pmgducati/Arcade-Project/Arcade Images/2020-11-22.png

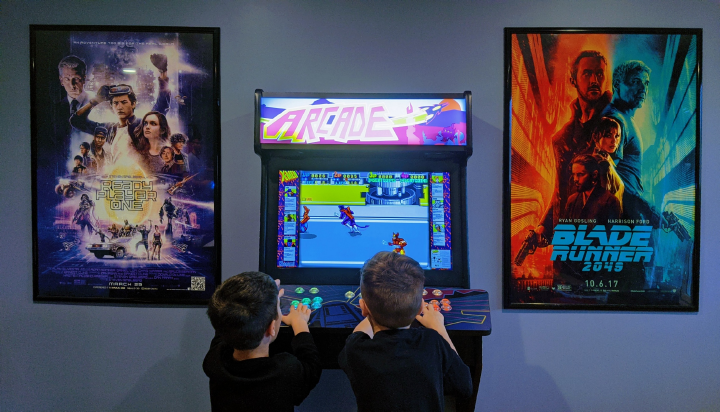
Arcade Images/2020-11-22.png
