pmgducati/Arcade-Project/Arcade Images/Cabinet - Bottom.png

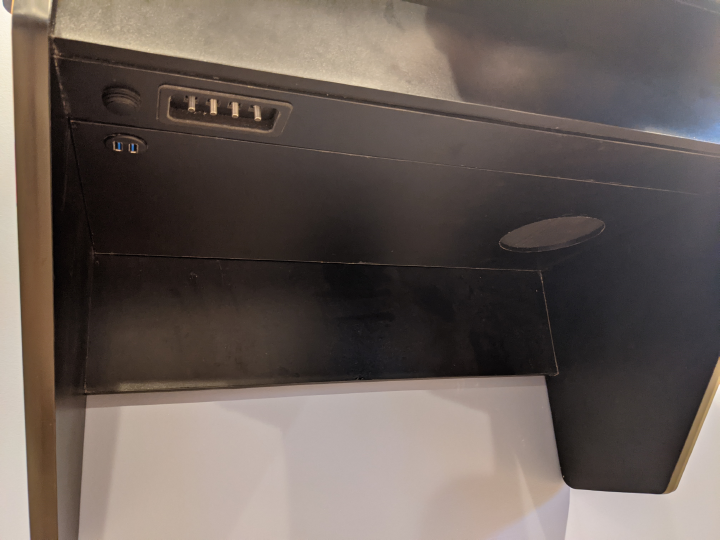
Arcade Images/Cabinet - Bottom.png
