pmgducati/Arcade-Project/Arcade Images/Cabinet - Front.png

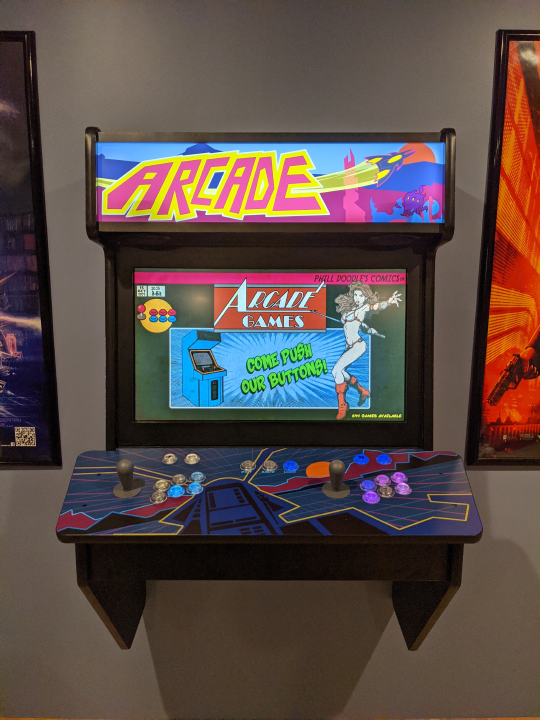
Arcade Images/Cabinet - Front.png
