pmgducati/Arcade-Project/Arcade Images/Cabinet - Left.png

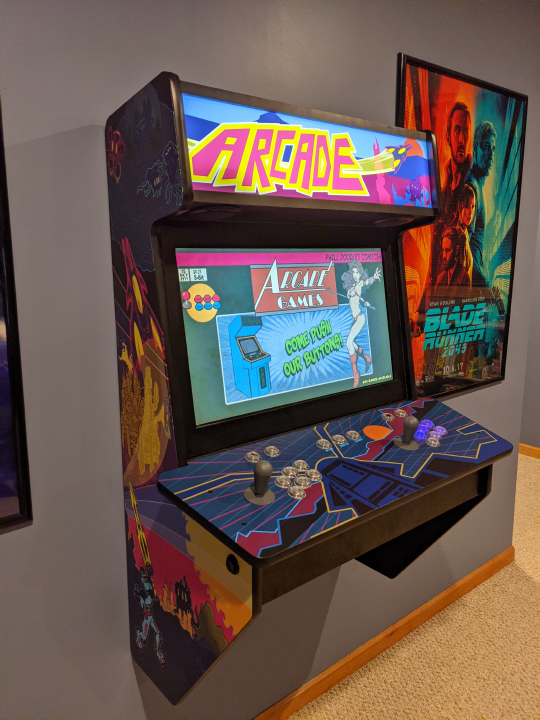
Arcade Images/Cabinet - Left.png
