pmgducati/Arcade-Project/Arcade Images/Cabinet - Right.png

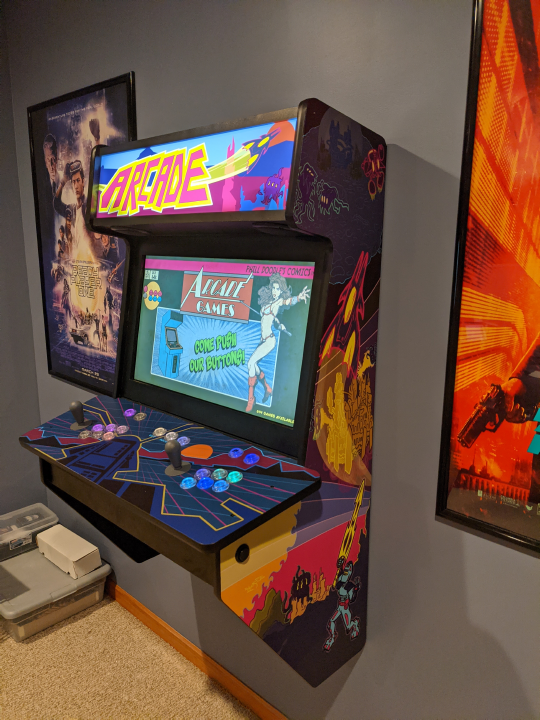
Arcade Images/Cabinet - Right.png
