pmgducati/Arcade-Project/Arcade Images/Cabinet - Top.png

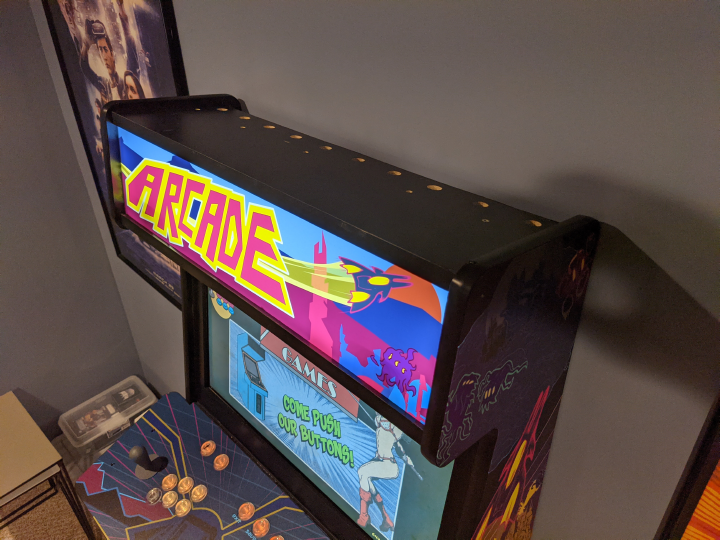
Arcade Images/Cabinet - Top.png
