pmgducati/Arcade-Project/Arcade Images/Control Panel.png

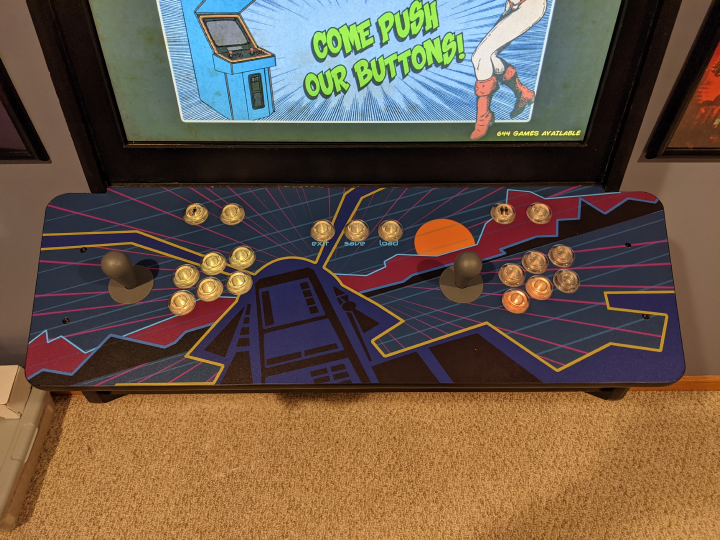
Arcade Images/Control Panel.png
