pmgducati/Arcade-Project/Arcade Images/Marquee.png

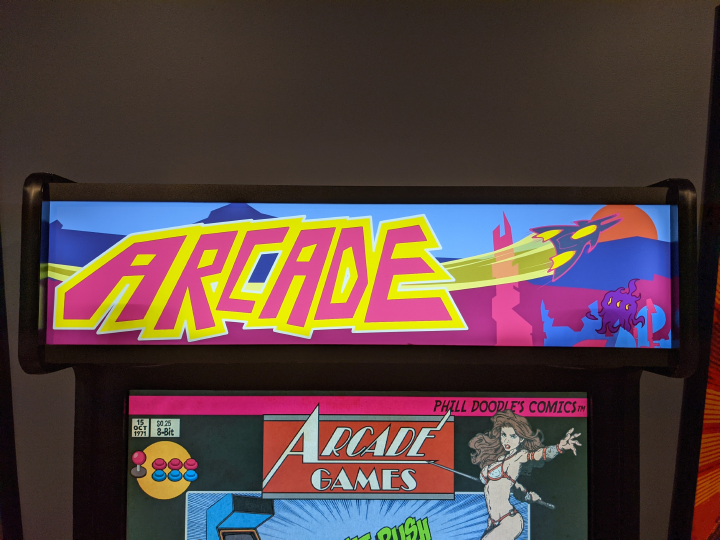
Arcade Images/Marquee.png
