pmgducati/Arcade-Project/Arcade Images/PXL_20201201_182632411.png

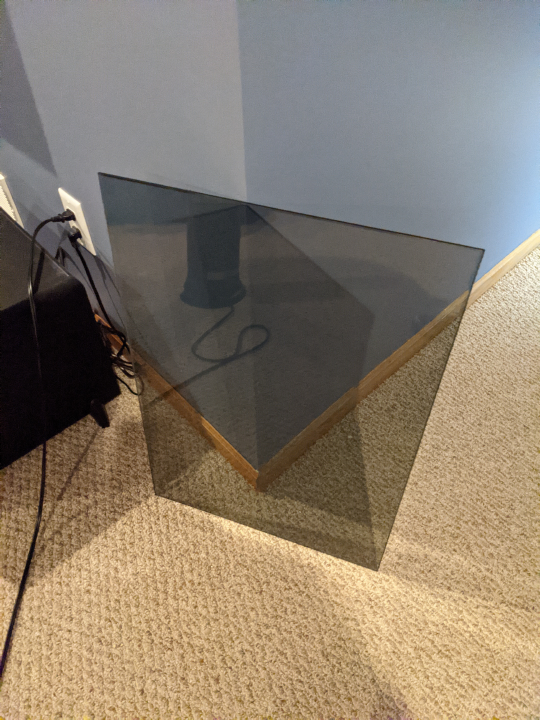
Arcade Images/PXL_20201201_182632411.png
