pmgducati/Arcade-Project/Arcade Images/PXL_20201201_213955558.png

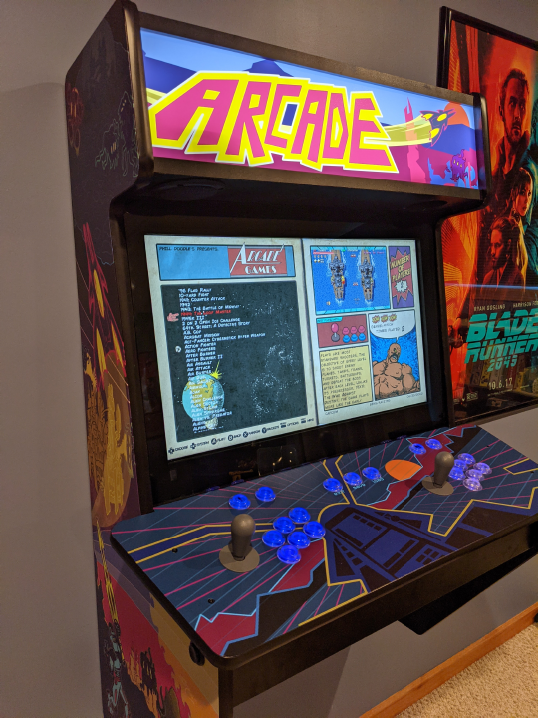
Arcade Images/PXL_20201201_213955558.png
