pmgducati/Arcade-Project/Arcade Images/PXL_20201201_214026619.png

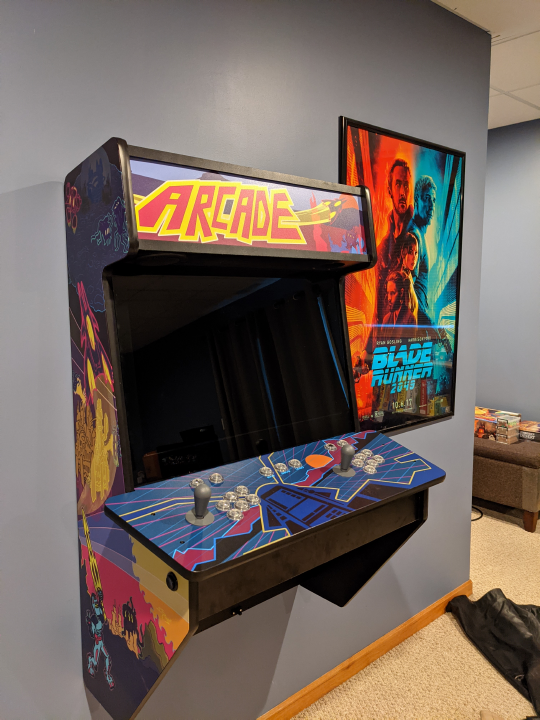
Arcade Images/PXL_20201201_214026619.png
