pmgducati/Arcade-Project/Arcade Images/Under Control Panel 1.png

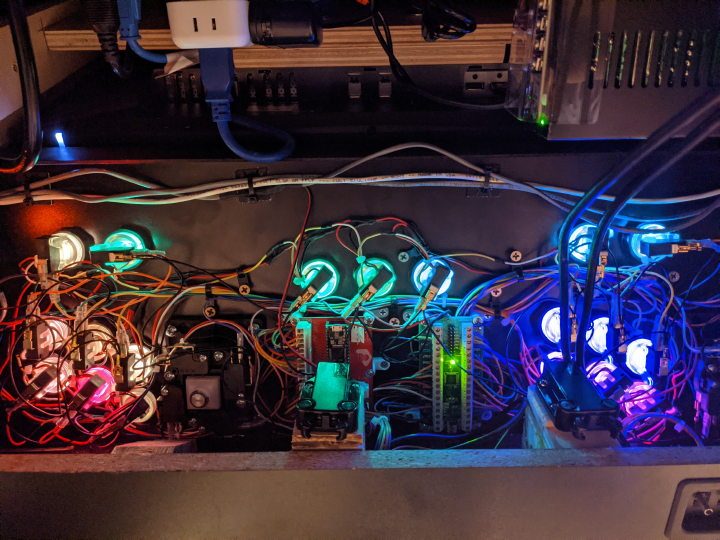
Arcade Images/Under Control Panel 1.png
