pmgducati/Arcade-Project/Arcade Images/Under Control Panel 2.png

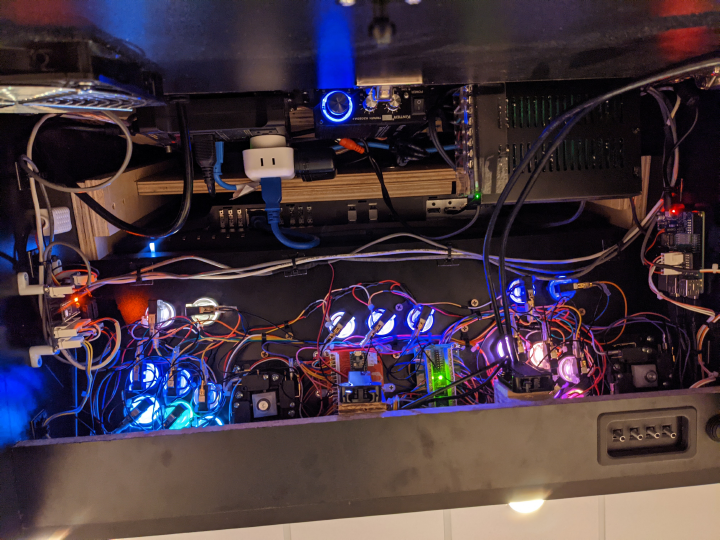
Arcade Images/Under Control Panel 2.png
