pmgducati/Arcade-Project/Art for Inspiration/1.jpg

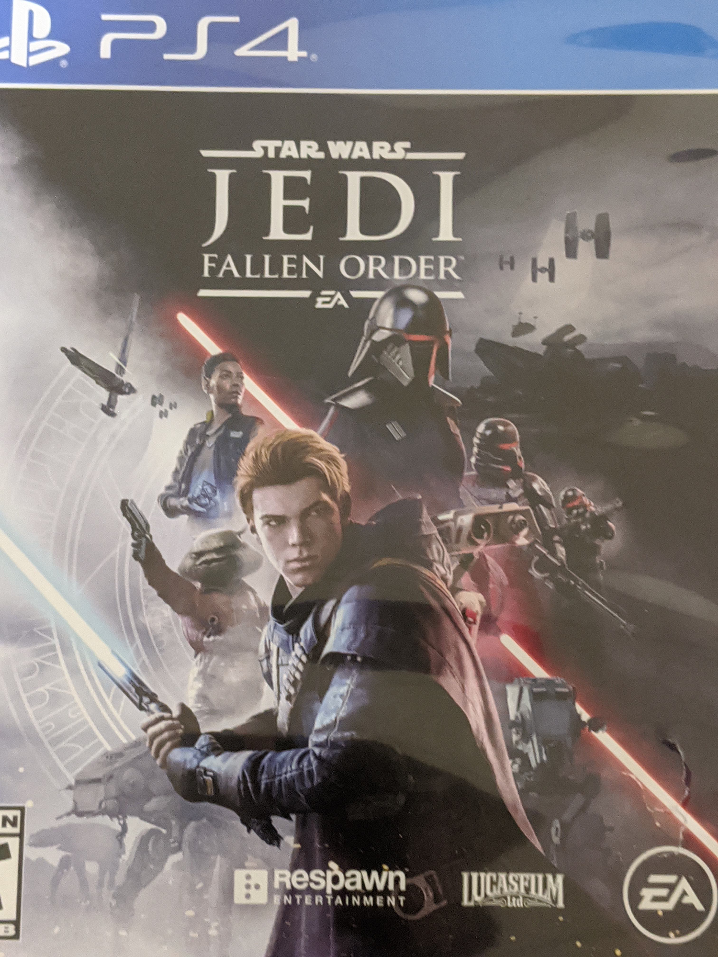
Art for Inspiration/1.jpg
