pmgducati/Arcade-Project/Art for Inspiration/17.png

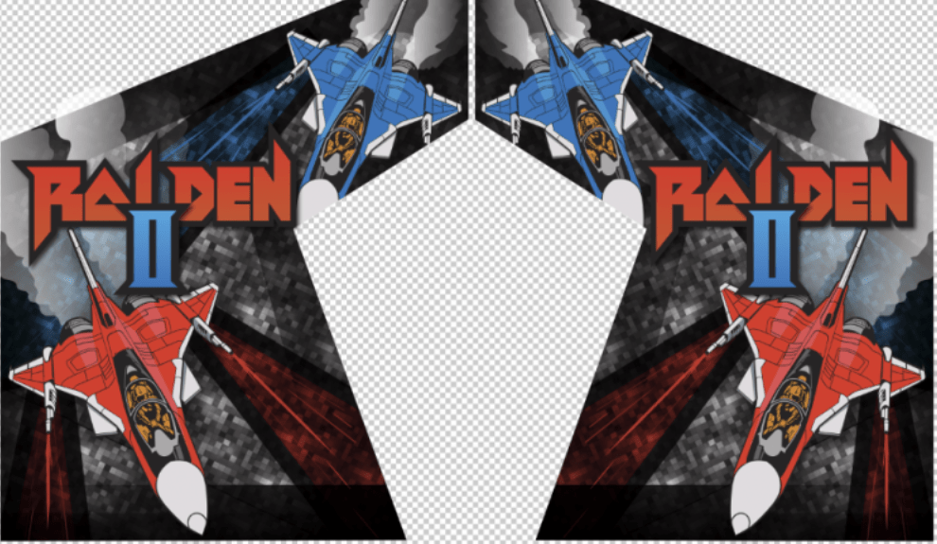
Art for Inspiration/17.png
