pmgducati/Arcade-Project/Art for Inspiration/18.jpg

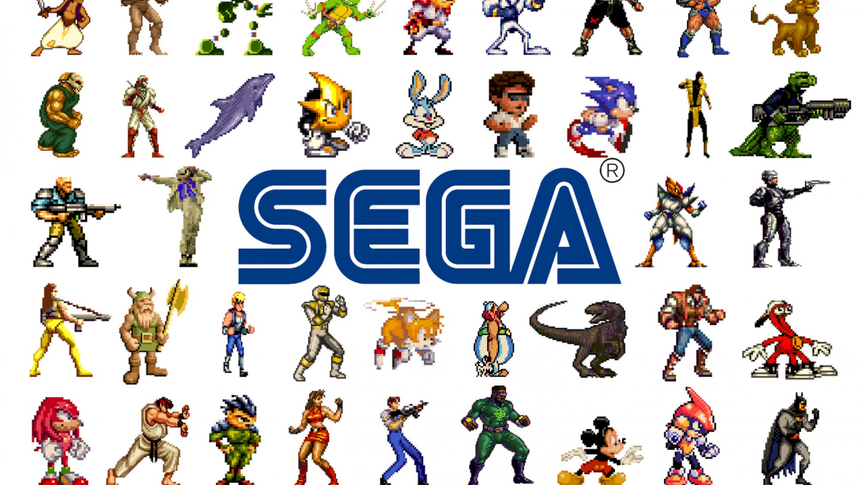
Art for Inspiration/18.jpg
