pmgducati/Arcade-Project/Art for Inspiration/19.jpg

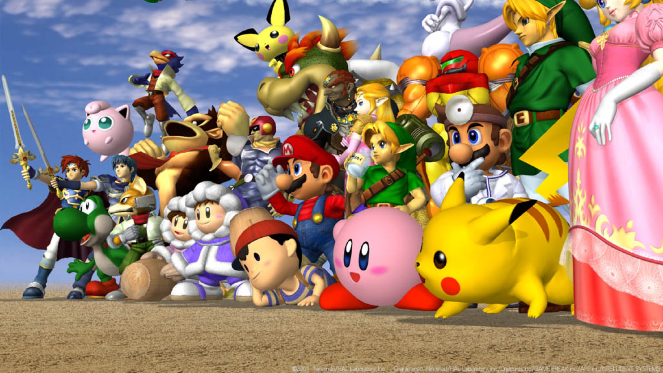
Art for Inspiration/19.jpg
