pmgducati/Arcade-Project/Art for Inspiration/20.jpg

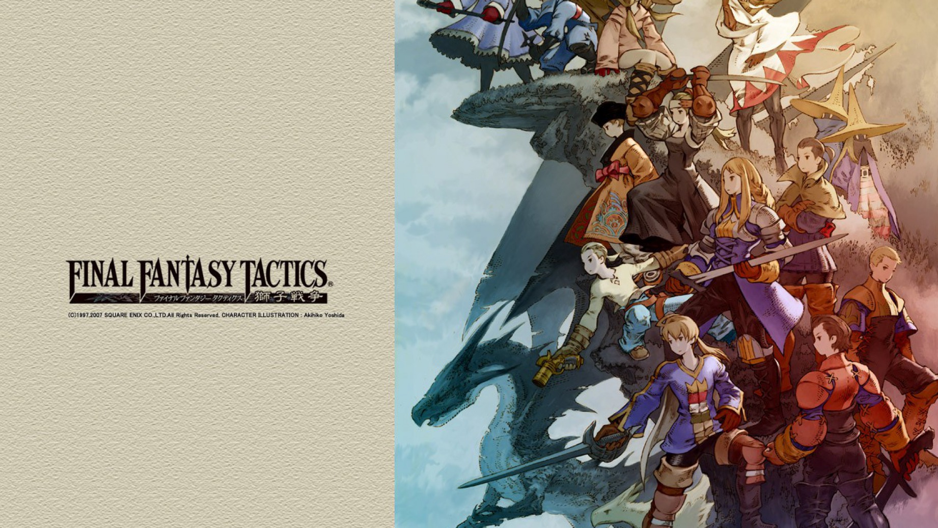
Art for Inspiration/20.jpg
