pmgducati/Arcade-Project/Art for Inspiration/21.jpg

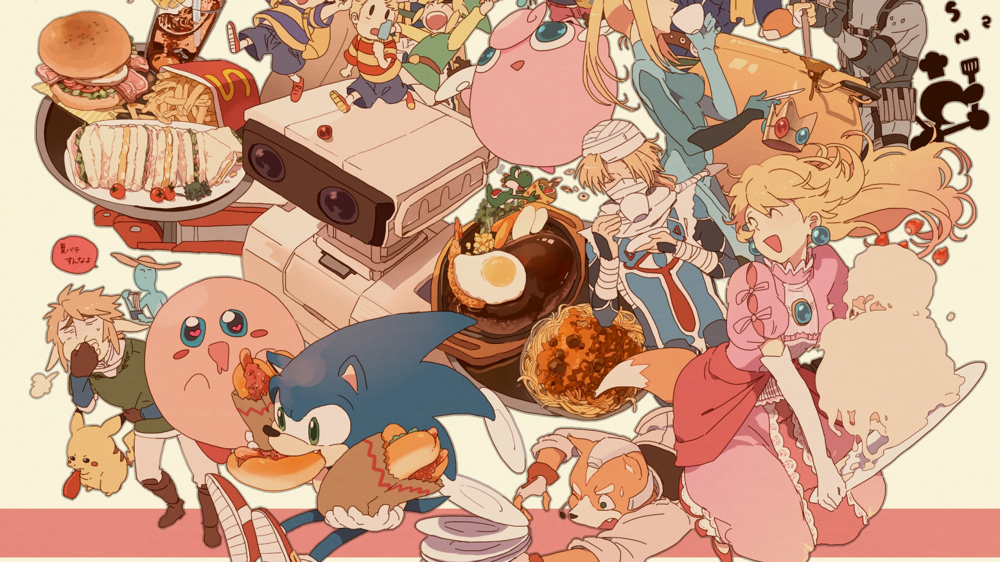
Art for Inspiration/21.jpg
