pmgducati/Arcade-Project/Art for Inspiration/22.jpg

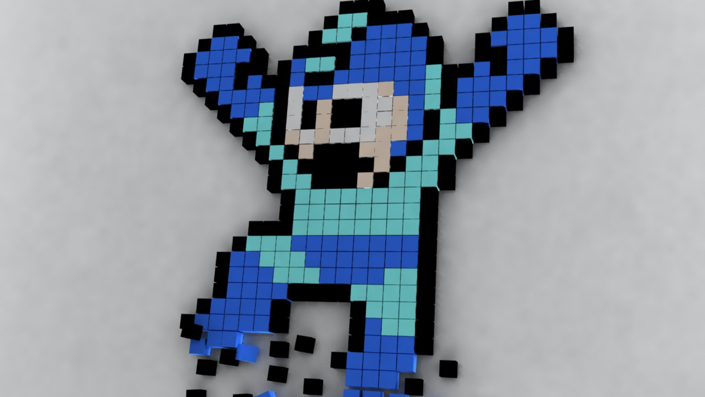
Art for Inspiration/22.jpg
