pmgducati/Arcade-Project/Art for Inspiration/23.jpg

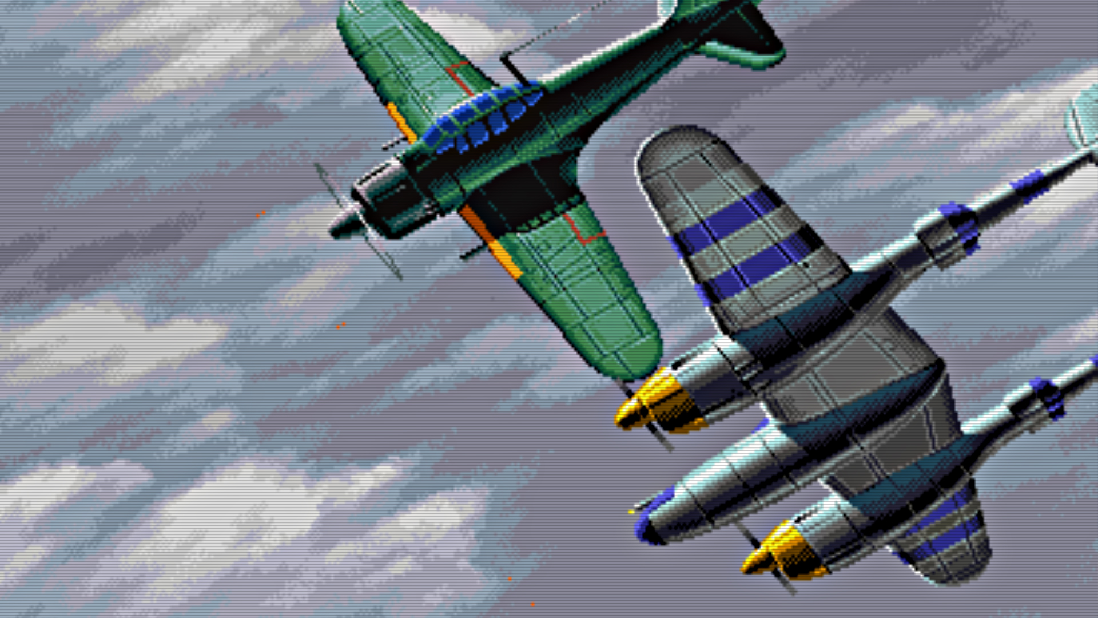
Art for Inspiration/23.jpg
