pmgducati/Arcade-Project/Art for Inspiration/24.jpg

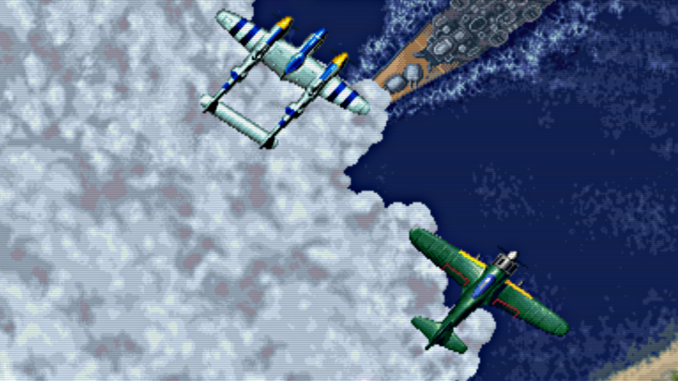
Art for Inspiration/24.jpg
