pmgducati/Arcade-Project/Art for Inspiration/26.jpg

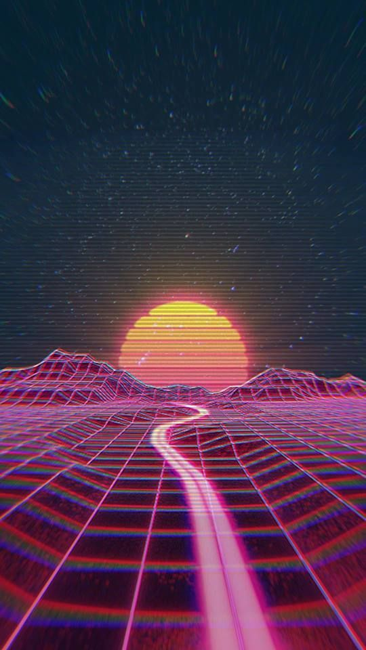
Art for Inspiration/26.jpg
