pmgducati/Arcade-Project/Art for Inspiration/27.jpg

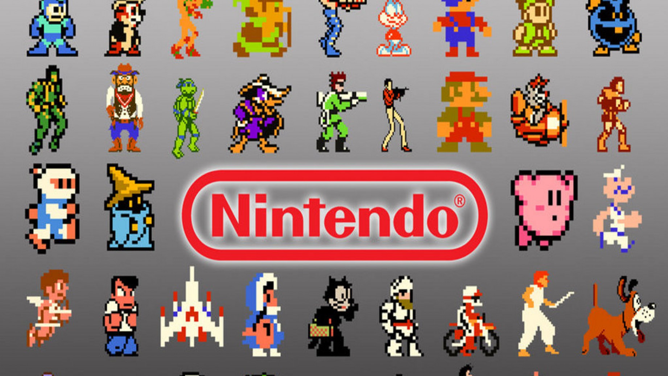
Art for Inspiration/27.jpg
