pmgducati/Arcade-Project/Art for Inspiration/28.jpg

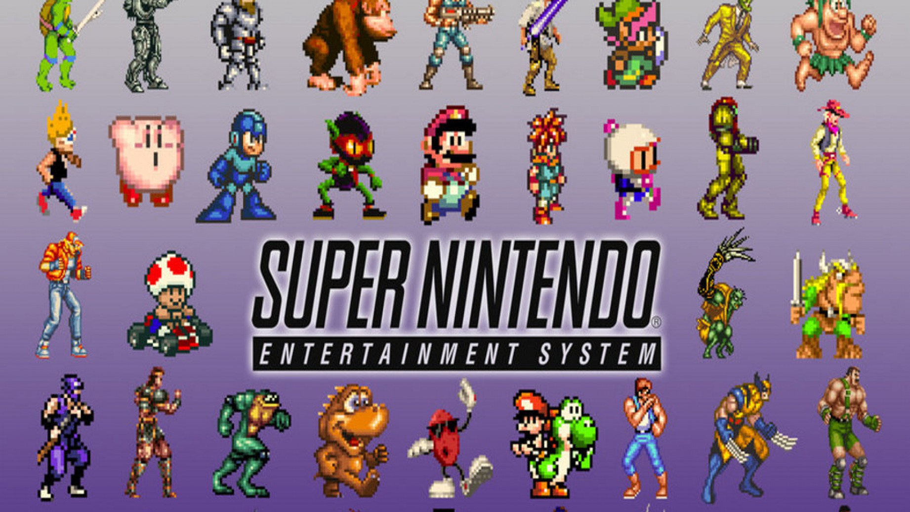
Art for Inspiration/28.jpg
