pmgducati/Arcade-Project/Art for Inspiration/29.jpg

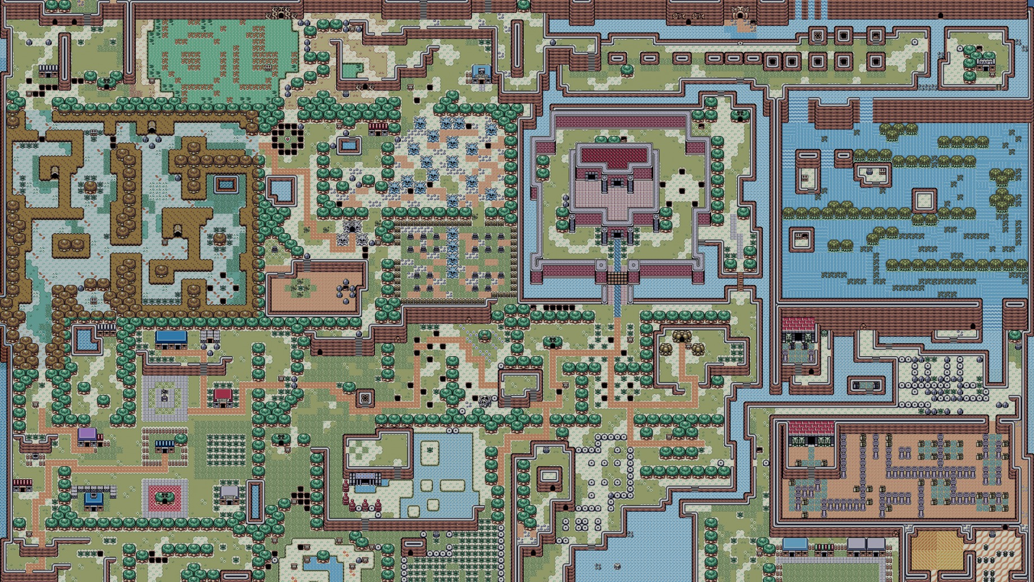
Art for Inspiration/29.jpg
