pmgducati/Arcade-Project/Art for Inspiration/32.jpg

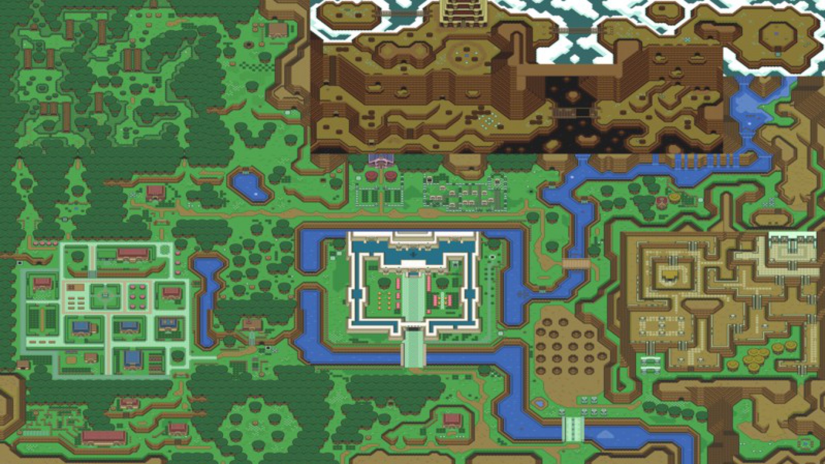
Art for Inspiration/32.jpg
