pmgducati/Arcade-Project/Art for Inspiration/33.jpg

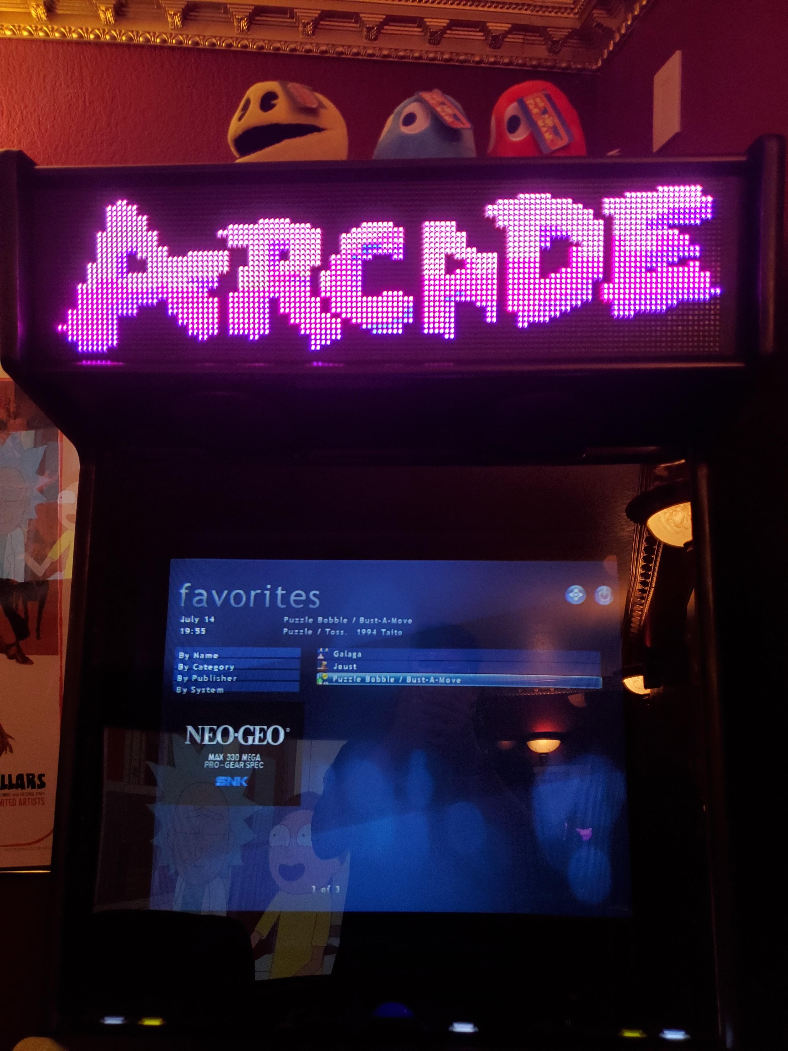
Art for Inspiration/33.jpg
