pmgducati/Arcade-Project/Art for Inspiration/39.jpg

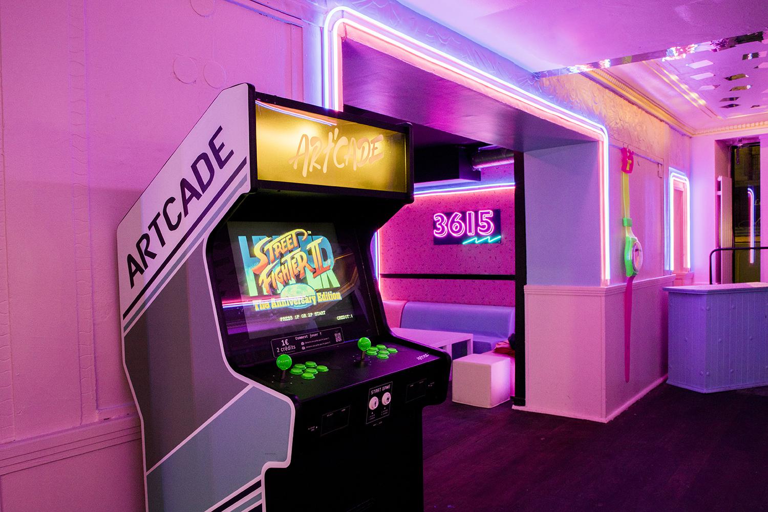
Art for Inspiration/39.jpg
