pmgducati/Arcade-Project/Art for Inspiration/40.jpg

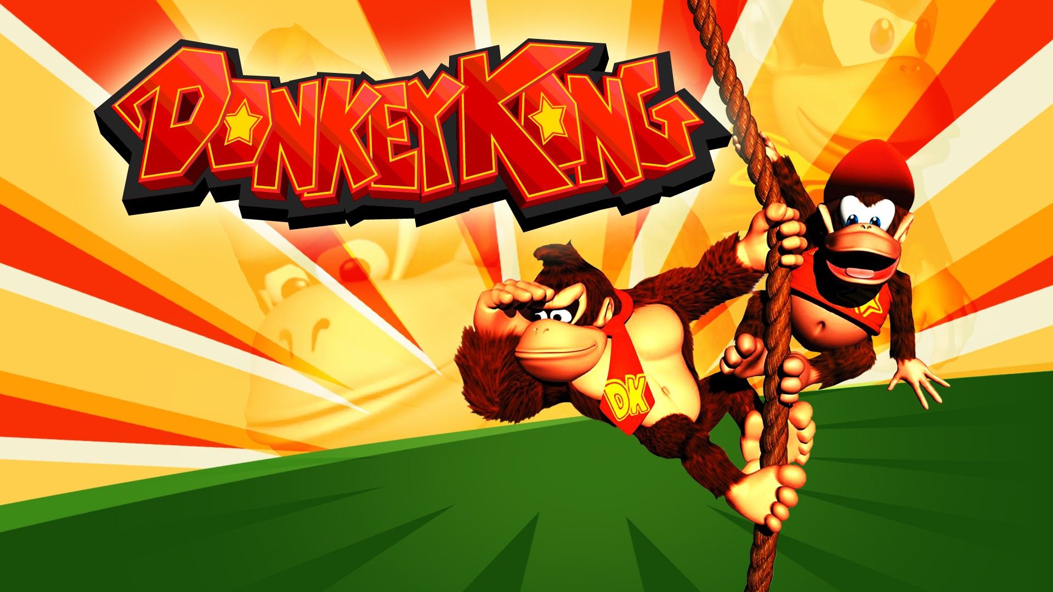
Art for Inspiration/40.jpg
