pmgducati/Arcade-Project/Art for Inspiration/42.jpg

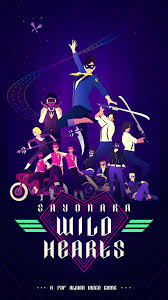
Art for Inspiration/42.jpg
