pmgducati/Arcade-Project/Art for Inspiration/43.jpg

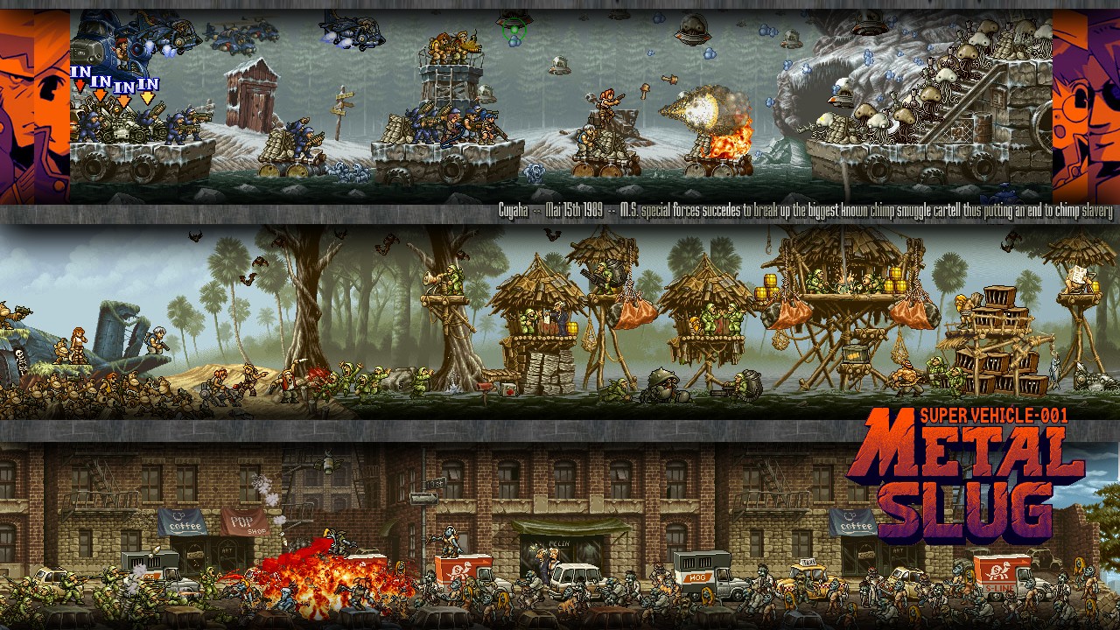
Art for Inspiration/43.jpg
