pmgducati/Arcade-Project/Art for Inspiration/44.jpg

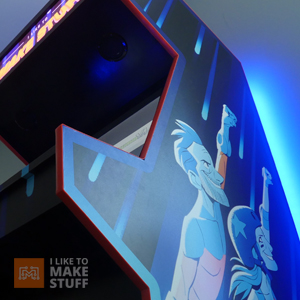
Art for Inspiration/44.jpg
