pmgducati/Arcade-Project/Art for Inspiration/45.jpg

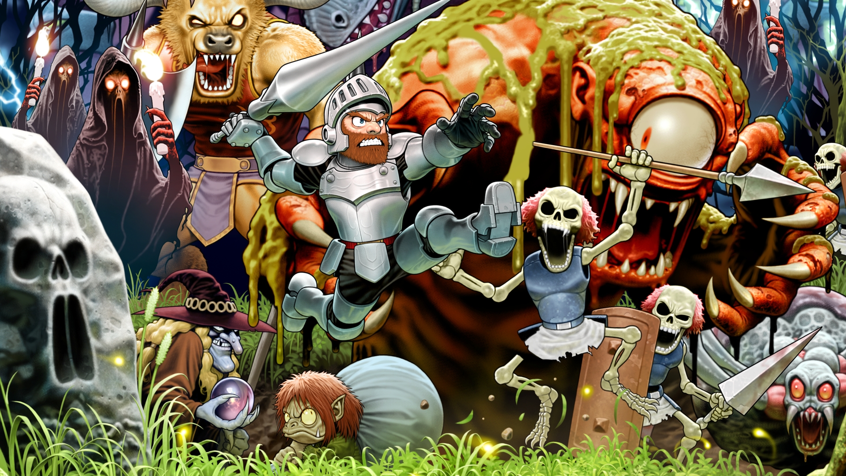
Art for Inspiration/45.jpg
