pmgducati/Arcade-Project/Art for Inspiration/46.jpg

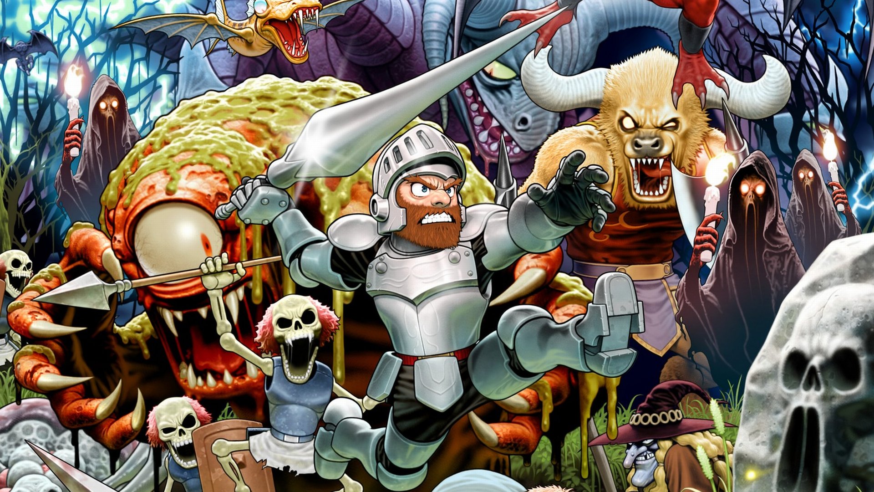
Art for Inspiration/46.jpg
