pmgducati/Arcade-Project/Art for Inspiration/48.jpg

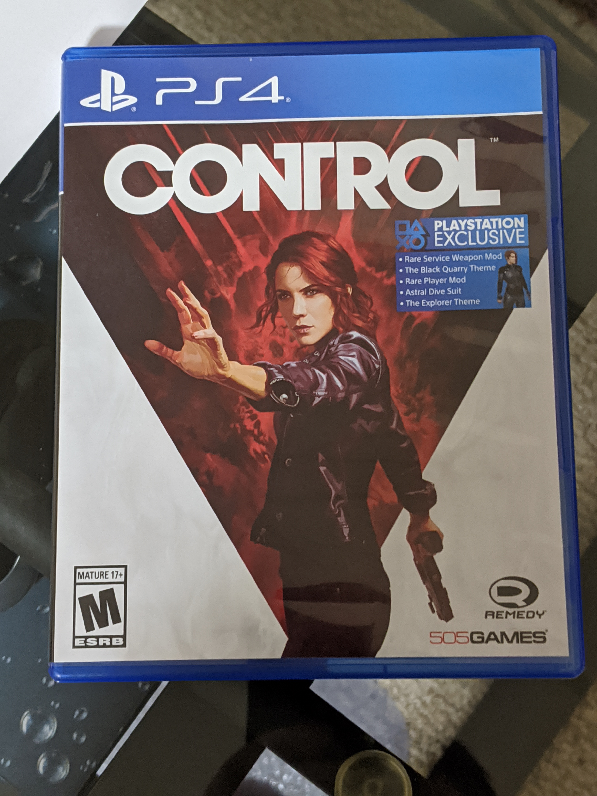
Art for Inspiration/48.jpg
