pmgducati/Arcade-Project/Art for Inspiration/49.jpg

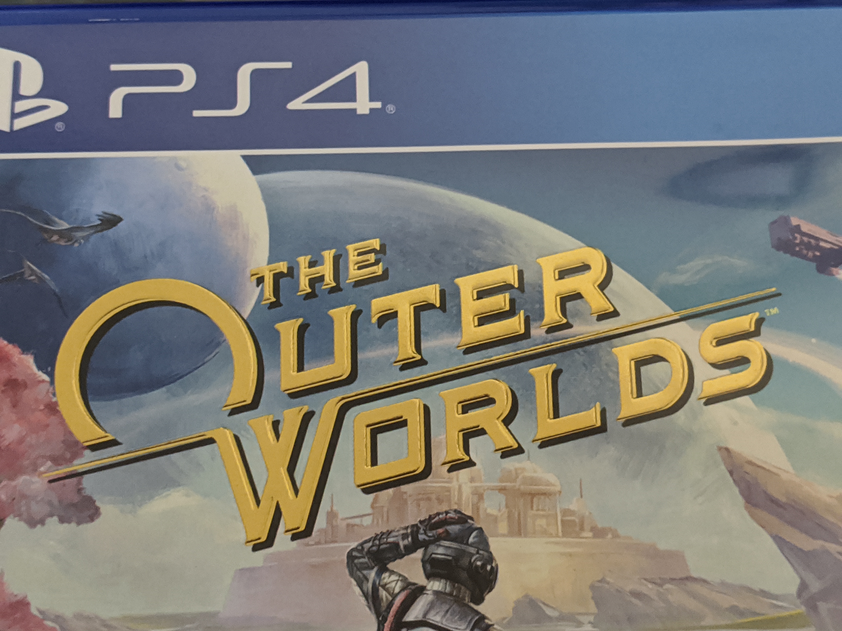
Art for Inspiration/49.jpg
