pmgducati/Arcade-Project/Art for Inspiration/72.jpg

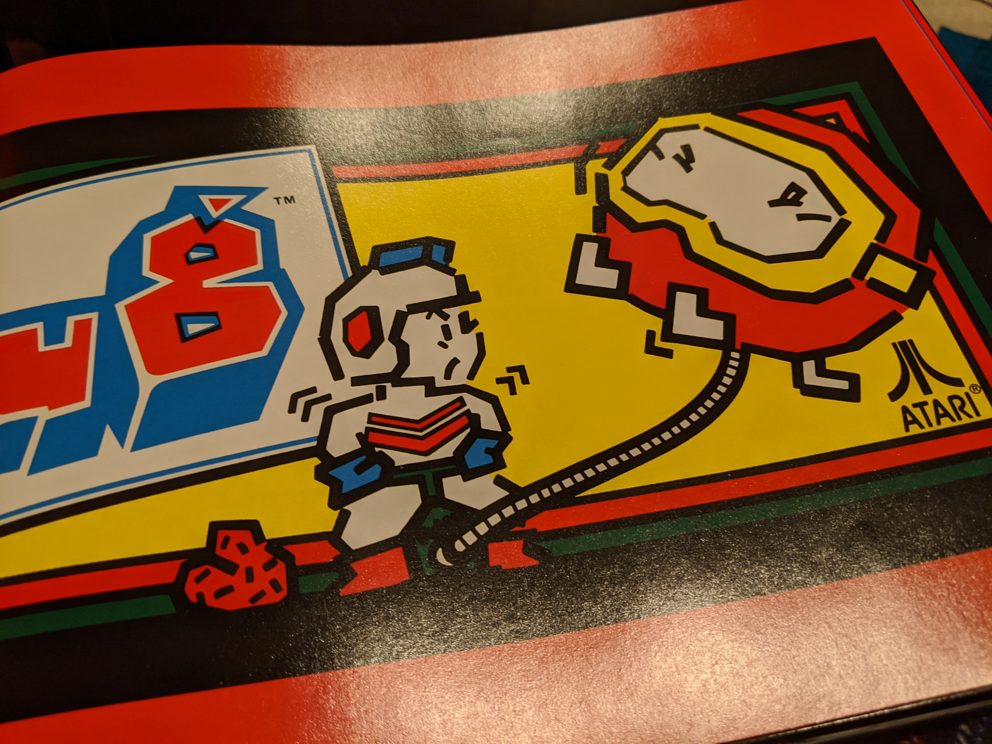
Art for Inspiration/72.jpg
