pmgducati/Arcade-Project/Art for Inspiration/85.jpg

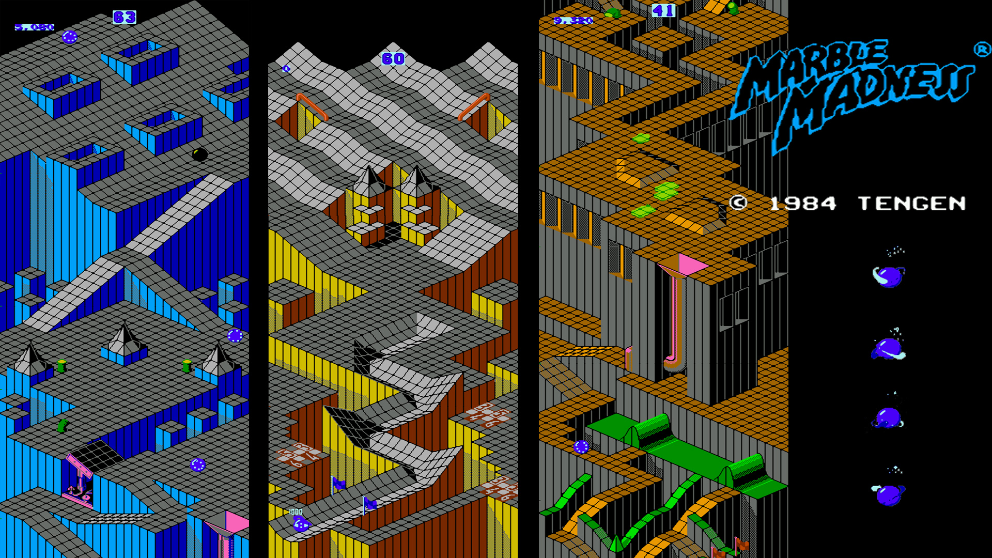
Art for Inspiration/85.jpg
