pmgducati/Arcade-Project/Art for Inspiration/86.jpg

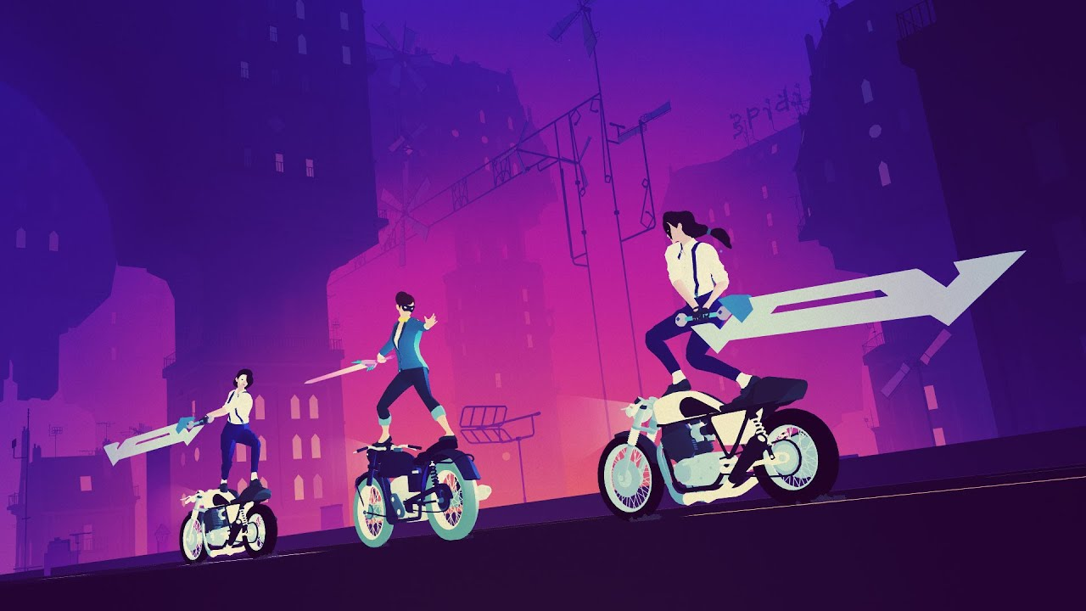
Art for Inspiration/86.jpg
