pmgducati/Arcade-Project/Art for Inspiration/87.jpg

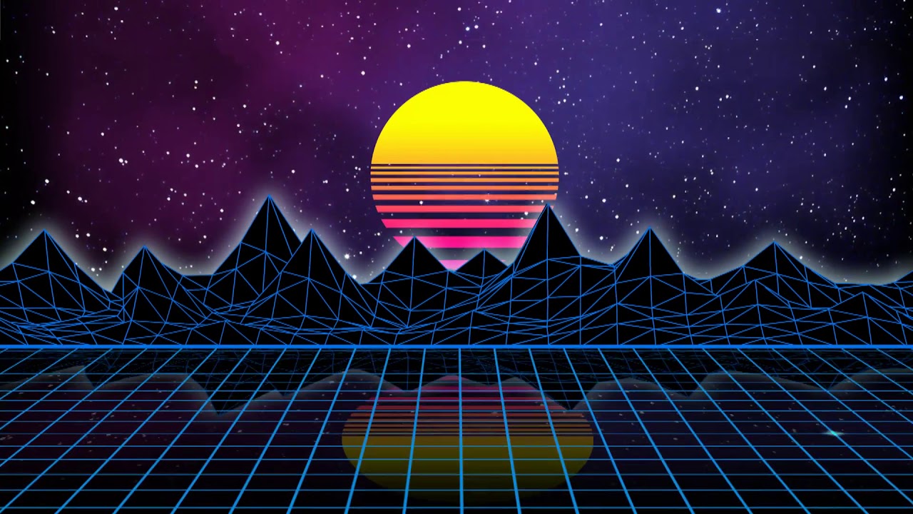
Art for Inspiration/87.jpg
