pmgducati/Arcade-Project/Art for Inspiration/89.jpg

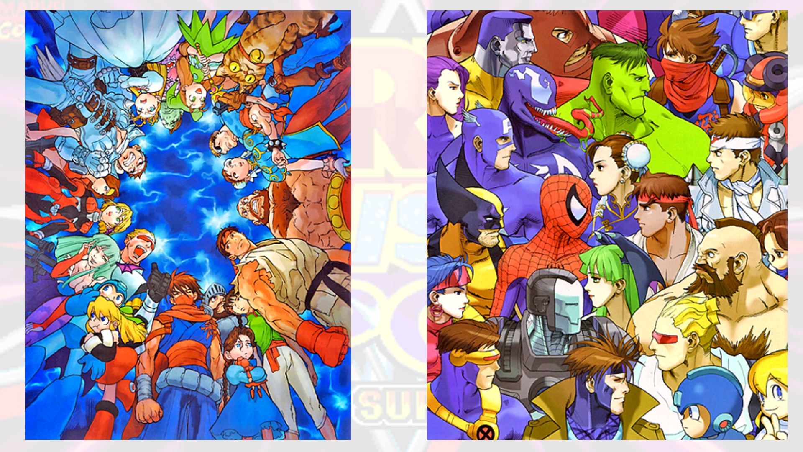
Art for Inspiration/89.jpg
