pmgducati/Arcade-Project/Art for Inspiration/90.jpg

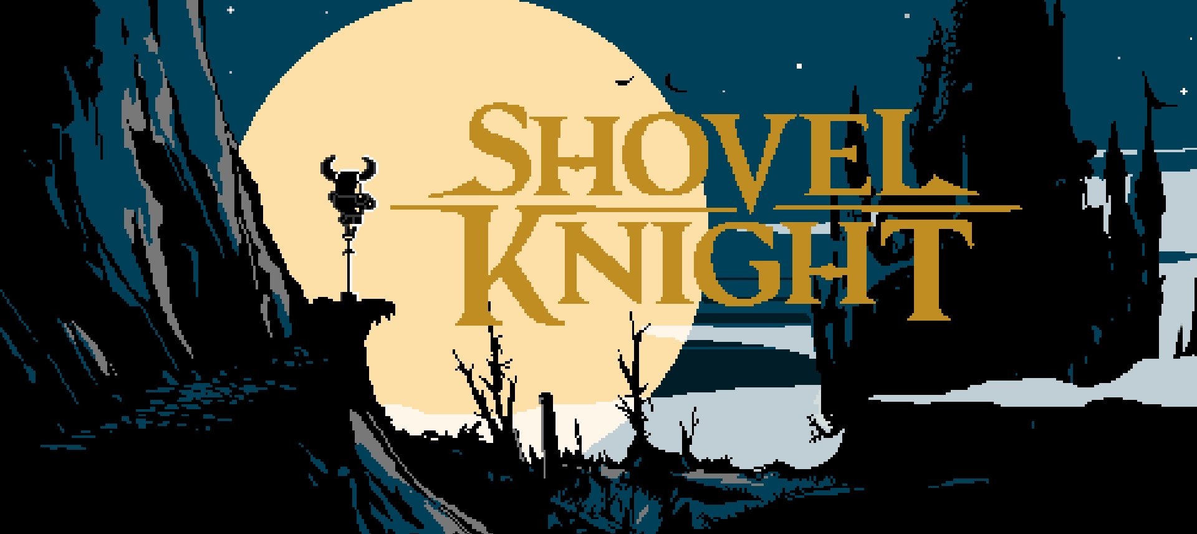
Art for Inspiration/90.jpg
