pmgducati/Arcade-Project/Art for Inspiration/94.jpg

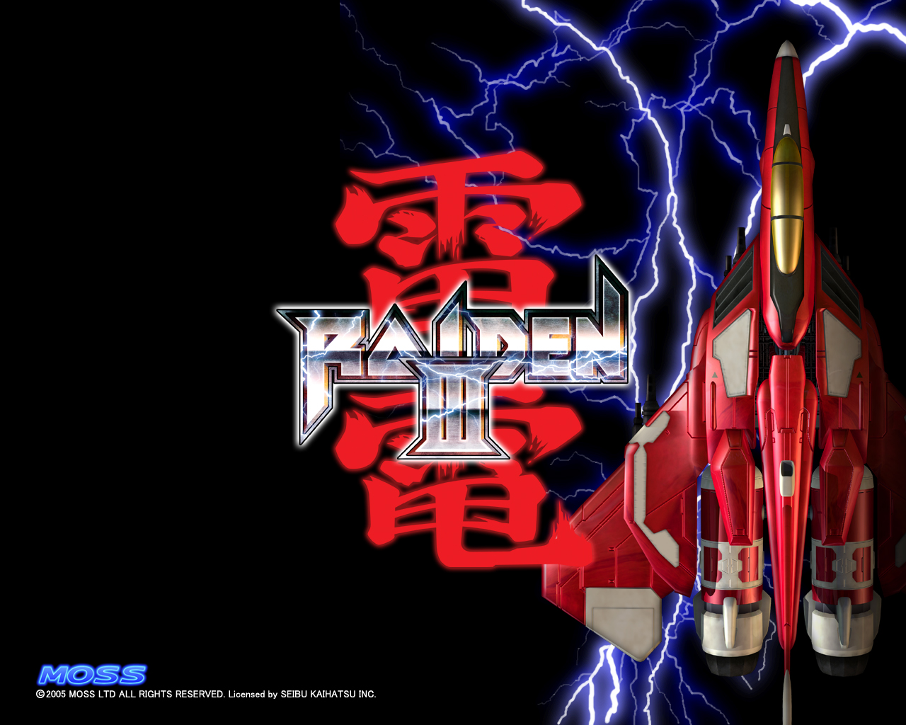
Art for Inspiration/94.jpg
