pmgducati/Arcade-Project/Art for Inspiration/97.png

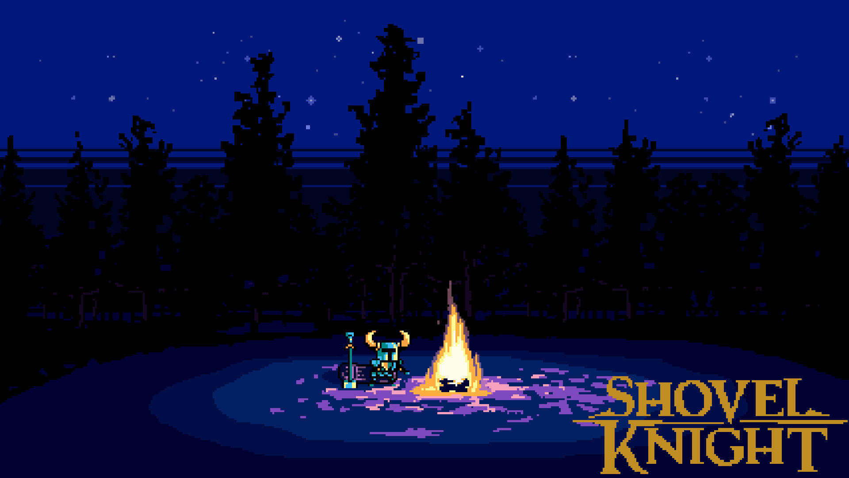
Art for Inspiration/97.png
