pmgducati/Arcade-Project/Art for Inspiration/98.jpg

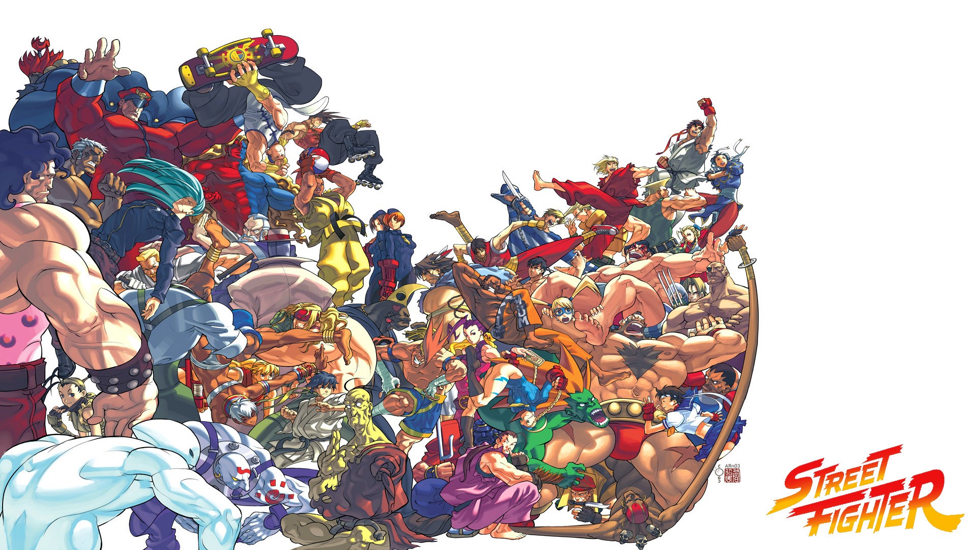
Art for Inspiration/98.jpg
