pmgducati/Arcade-Project/Art for Inspiration/99.jpg

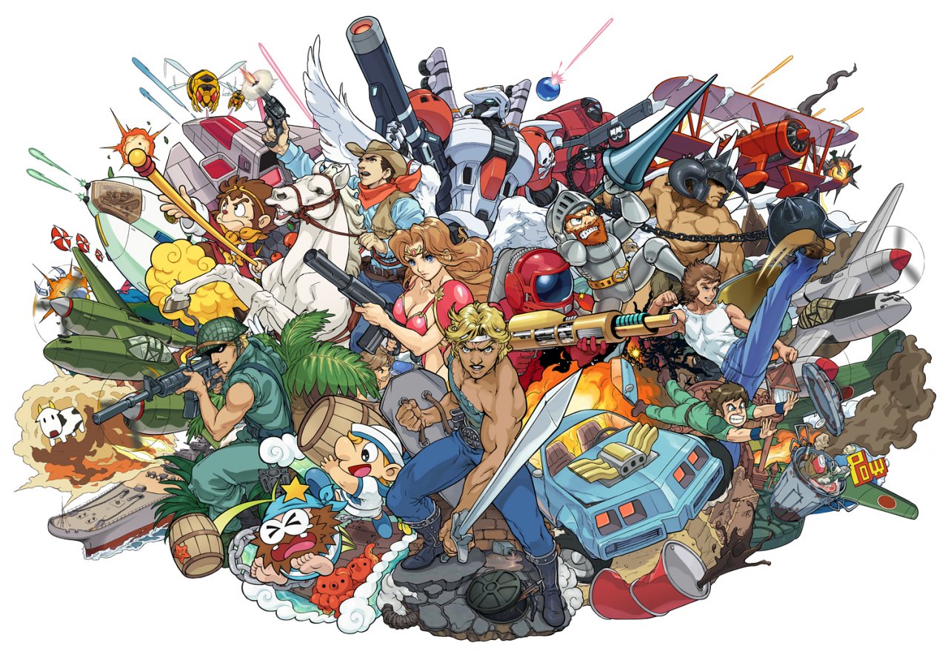
Art for Inspiration/99.jpg
