pmgducati/Arcade-Project/Art for Inspiration/100.jpg

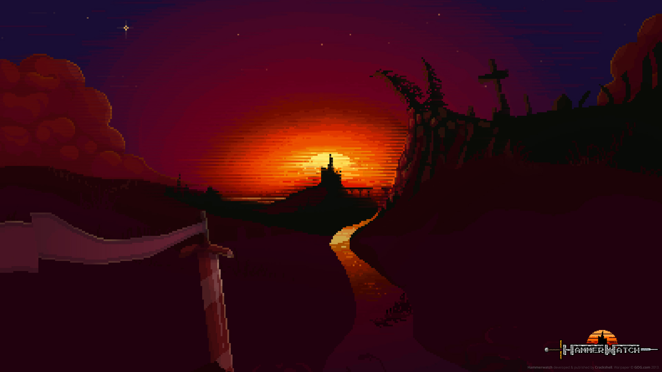
Art for Inspiration/100.jpg
