pmgducati/Arcade-Project/Art for Inspiration/101.jpg

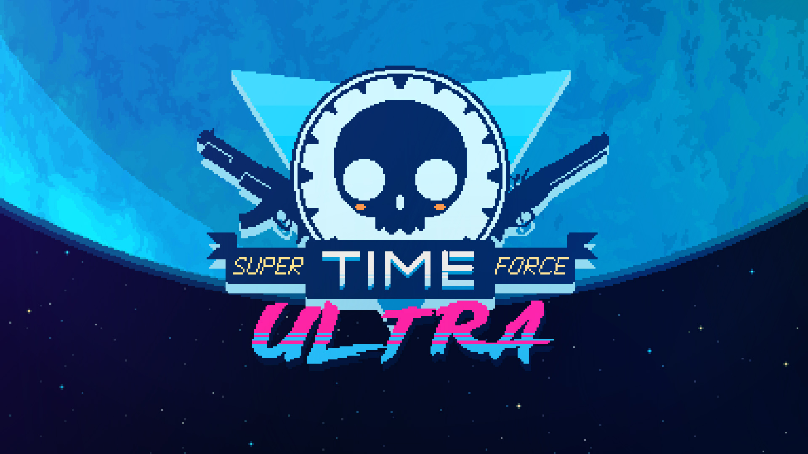
Art for Inspiration/101.jpg
