pmgducati/Arcade-Project/Art for Inspiration/102.jpg

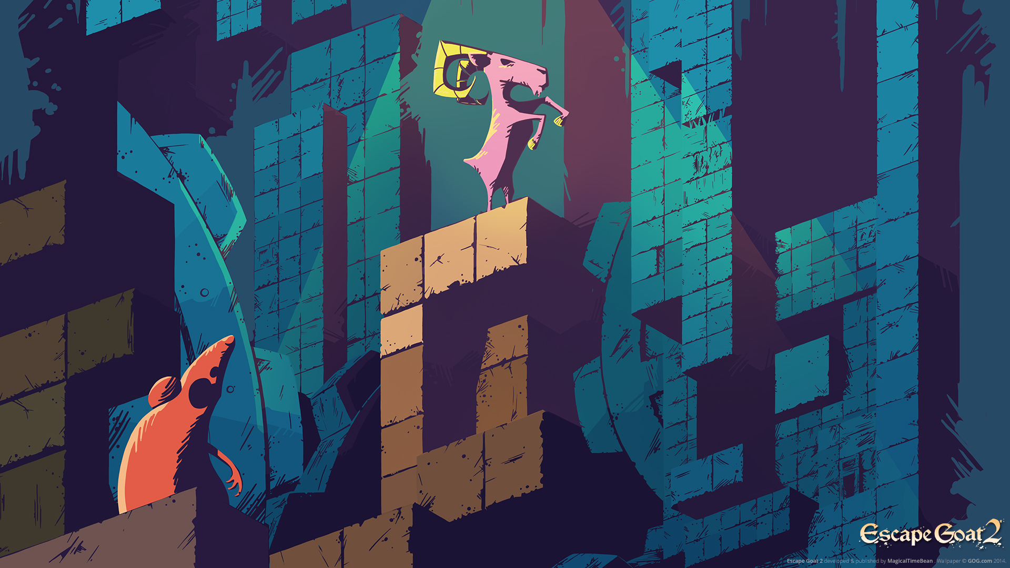
Art for Inspiration/102.jpg
