pmgducati/Arcade-Project/Art for Inspiration/103.jpg

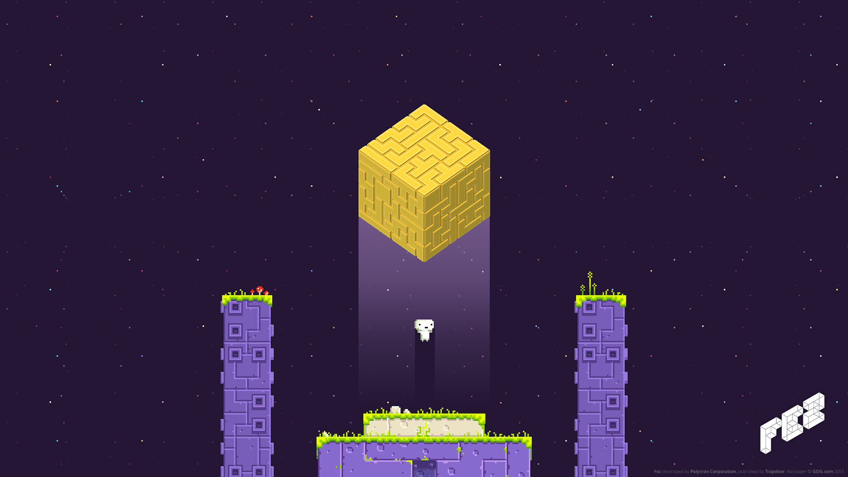
Art for Inspiration/103.jpg
