pmgducati/Arcade-Project/Art for Inspiration/104.jpg

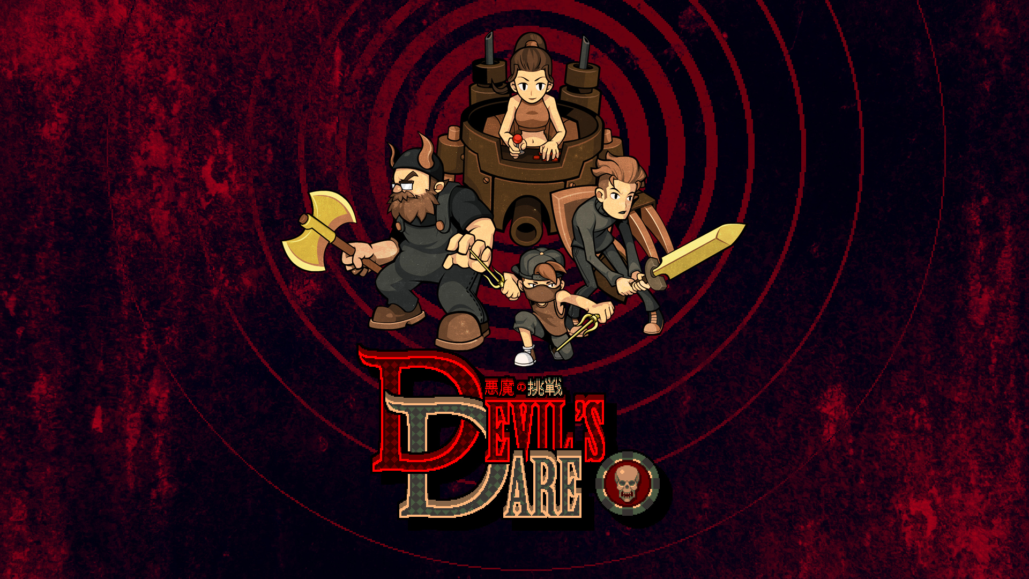
Art for Inspiration/104.jpg
