pmgducati/Arcade-Project/Art for Inspiration/105.png

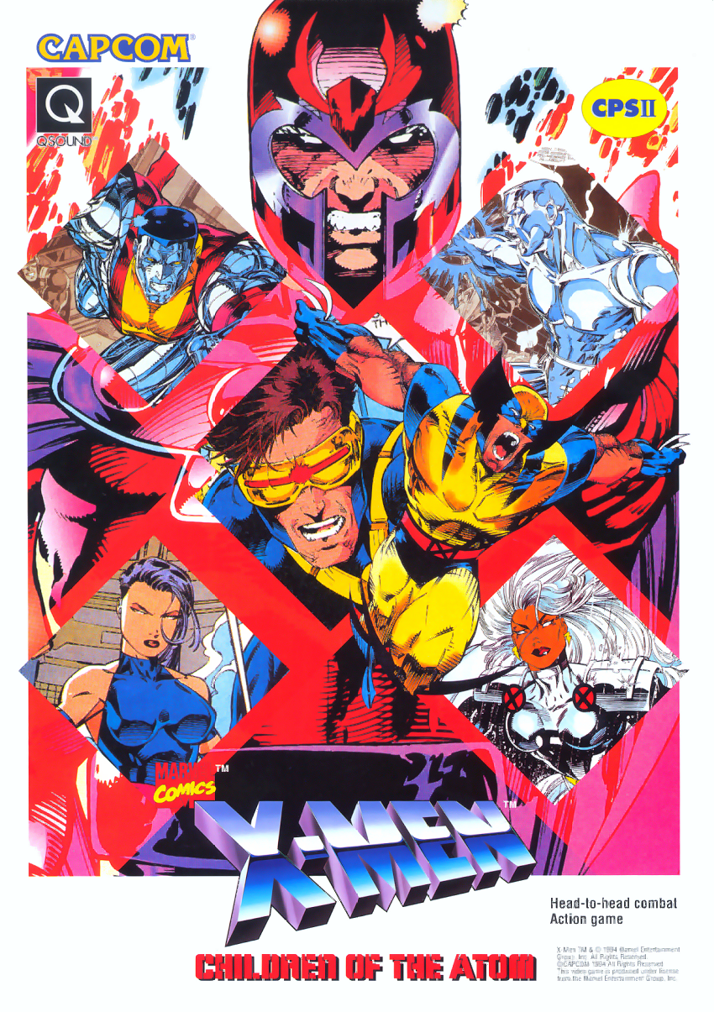
Art for Inspiration/105.png
