pmgducati/Arcade-Project/Art for Inspiration/107.jpg

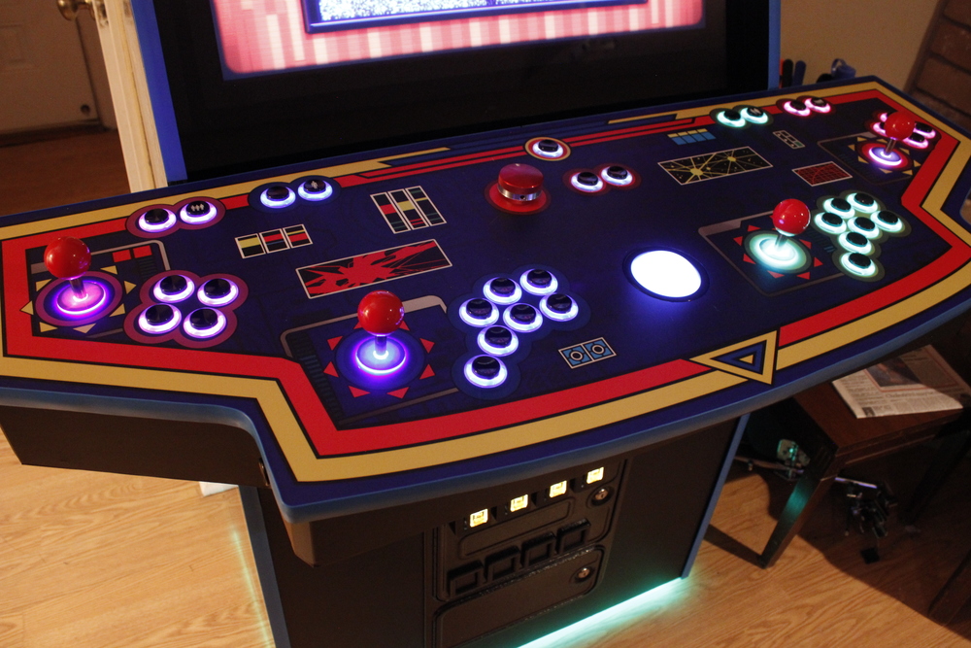
Art for Inspiration/107.jpg
