pmgducati/Arcade-Project/Code/Arcade_Control_LEDs/CHSV.jpg

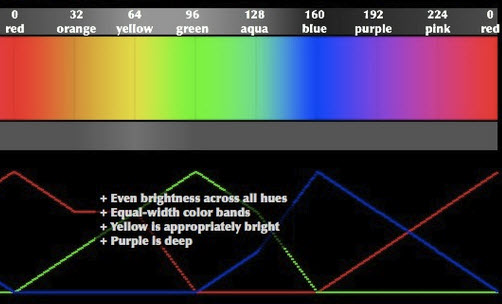
Code/Arcade_Control_LEDs/CHSV.jpg
