pmgducati/Arcade-Project/PCB Files/Grainy.bmp

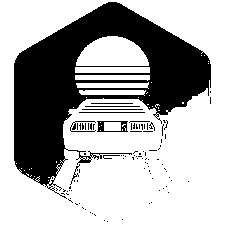
PCB Files/Grainy.bmp
