pmgducati/Arcade-Project/CAD Files/Reference Parts/4x8.SLDPRT

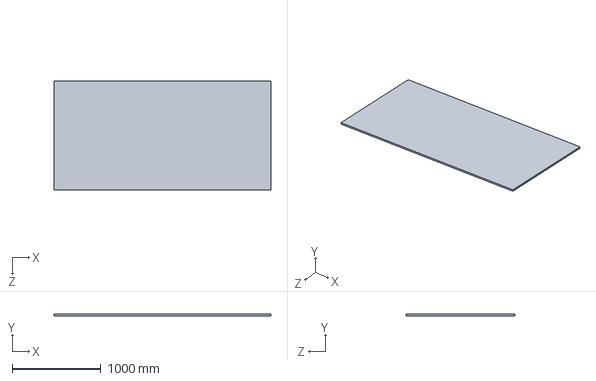
[picture p89: CAD file, 2026-02-07]
CAD Files/Reference Parts/4x8.SLDPRT
2438.4 x 19.1 x 1219.2 mm
