pmgducati/Arcade-Project/STLs and Gerbers/STL R2 (Updated)/STL for Plexi/Monitor Bezel.STL

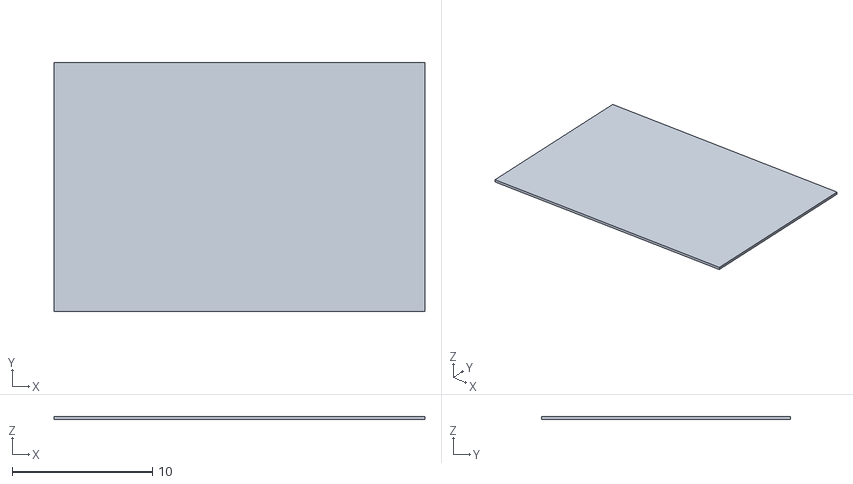
[picture p92: CAD file, 2020-11-29]
STLs and Gerbers/STL R2 (Updated)/STL for Plexi/Monitor Bezel.STL
26.4 x 17.8 x 0.236
