pmgducati/Arcade-Project/Art for Inspiration/AI Files/Decal Bezel.DXF

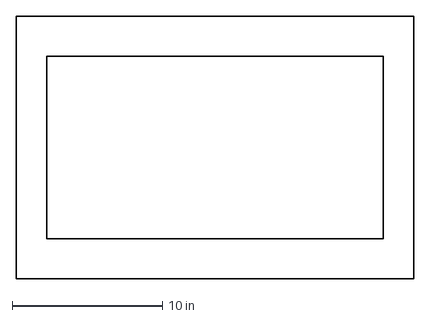
[picture p93: CAD file, 2020-04-03]
Art for Inspiration/AI Files/Decal Bezel.DXF
26.5 x 17.5 in
