pmgducati/Arcade-Project/CAD Files/Purchased Parts/Switch.SLDPRT

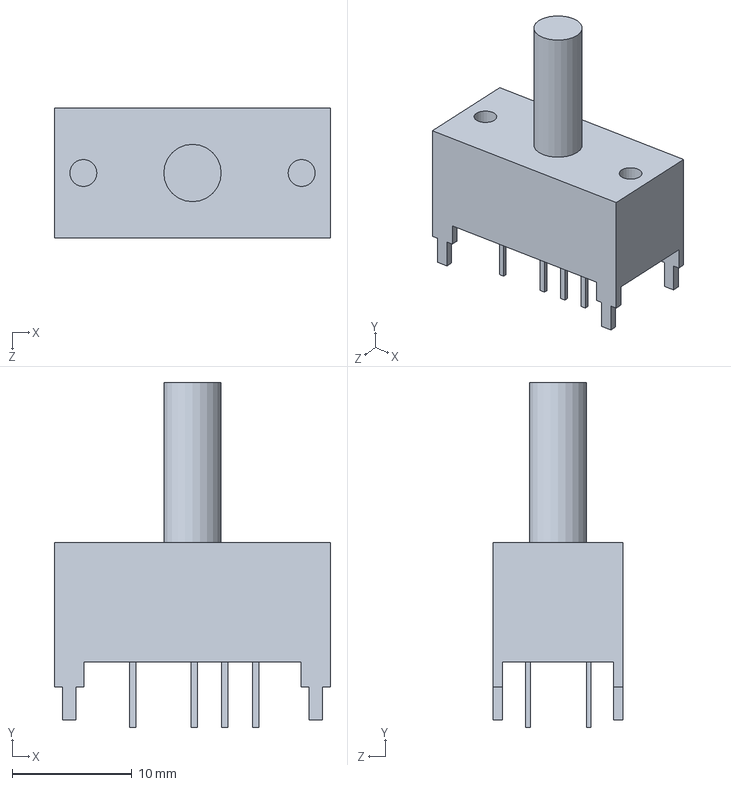
[picture p94: CAD file, 2026-02-07]
CAD Files/Purchased Parts/Switch.SLDPRT
23.1 x 28.8 x 10.8 mm
