pmgducati/Arcade-Project/CAD Files/Reference Parts/PCB.SLDPRT

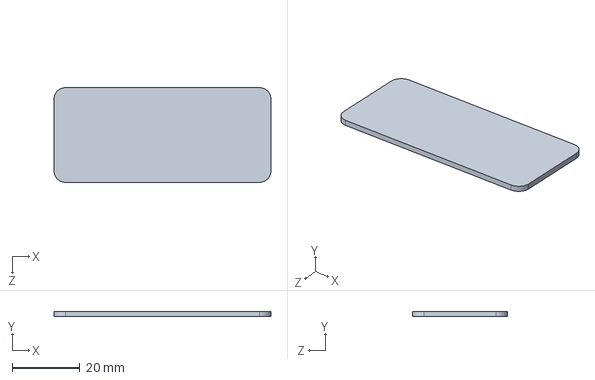
[picture p95: CAD file, 2026-02-07]
CAD Files/Reference Parts/PCB.SLDPRT
64.0 x 1.60 x 28.0 mm
