pmgducati/Arcade-Project/STLs and Gerbers/STL R1 for CNC (Manufactured)/Monitor Panel.STL

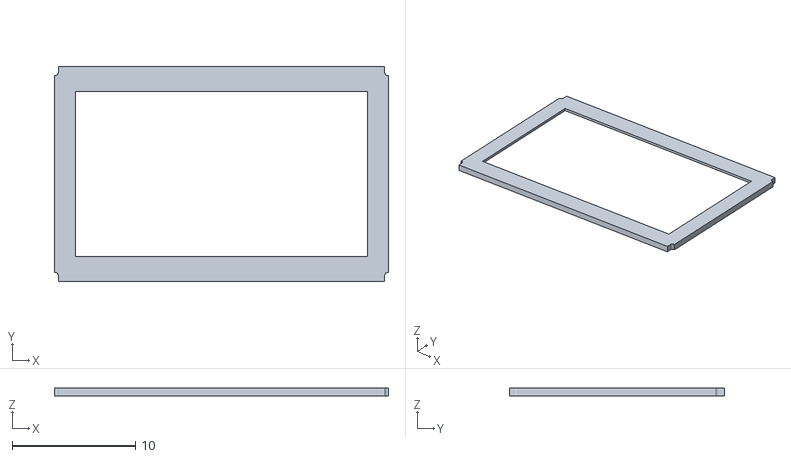
[picture p96: CAD file, 2020-04-03]
STLs and Gerbers/STL R1 for CNC (Manufactured)/Monitor Panel.STL
27.1 x 17.5 x 0.625
