pmgducati/Arcade-Project/STLs and Gerbers/STL R2 (Updated)/3D Printing/LCD Mount.STL

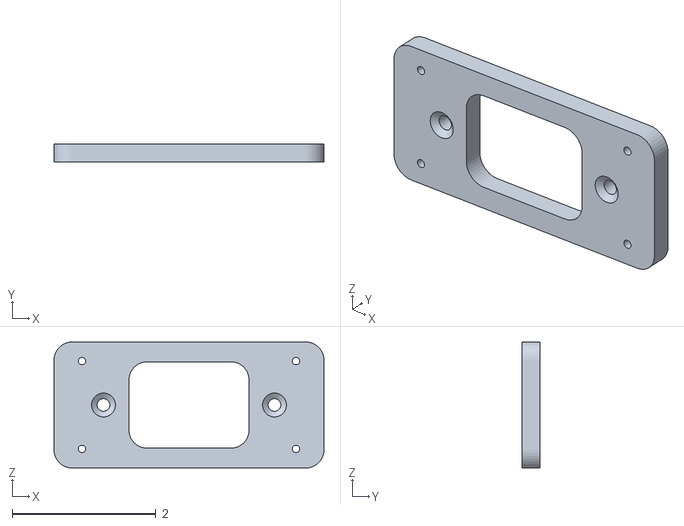
[picture p97: CAD file, 2021-04-09]
STLs and Gerbers/STL R2 (Updated)/3D Printing/LCD Mount.STL
3.75 x 0.25 x 1.75
