pmgducati/Arcade-Project/STLs and Gerbers/STL R2 (Updated)/Cleat - Wall.DXF

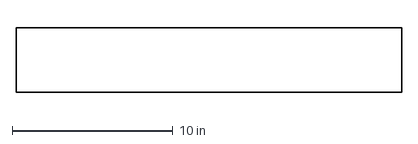
[picture p98: CAD file, 2025-06-07]
STLs and Gerbers/STL R2 (Updated)/Cleat - Wall.DXF
24.0 x 4.00 in
