pmgducati/Arcade-Project/Art for Inspiration/AI Files/Decal Marquee.DXF

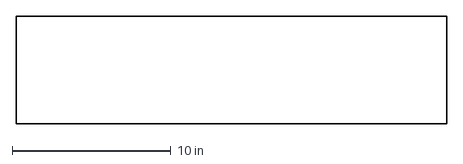
[picture p99: CAD file, 2020-04-03]
Art for Inspiration/AI Files/Decal Marquee.DXF
27.1 x 6.78 in
