pmgducati/Arcade-Project/CAD Files/Reference Parts/Speaker Grill.SLDPRT

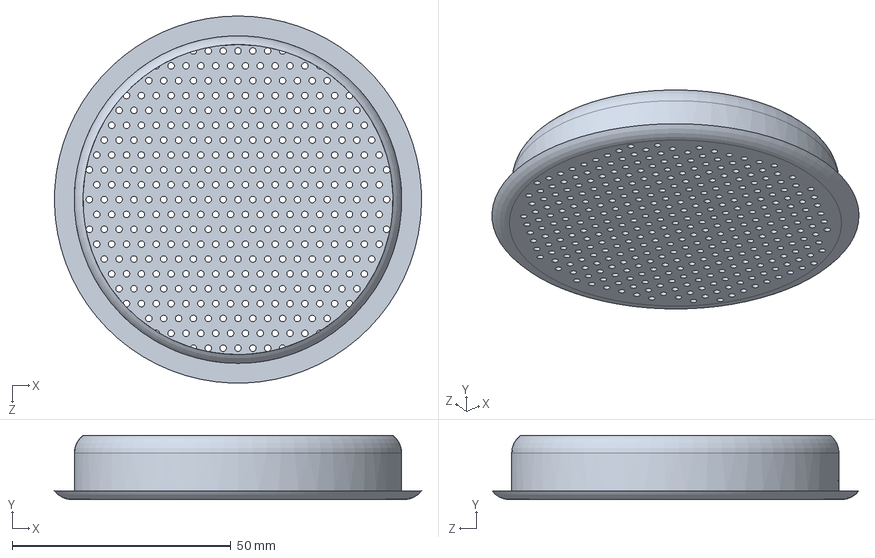
[picture p100: CAD file, 2020-04-03]
CAD Files/Reference Parts/Speaker Grill.SLDPRT
84.0 x 14.7 x 84.0 mm
