pmgducati/Arcade-Project/STLs and Gerbers/STL R1 for CNC (Manufactured)/Control Panel.STL

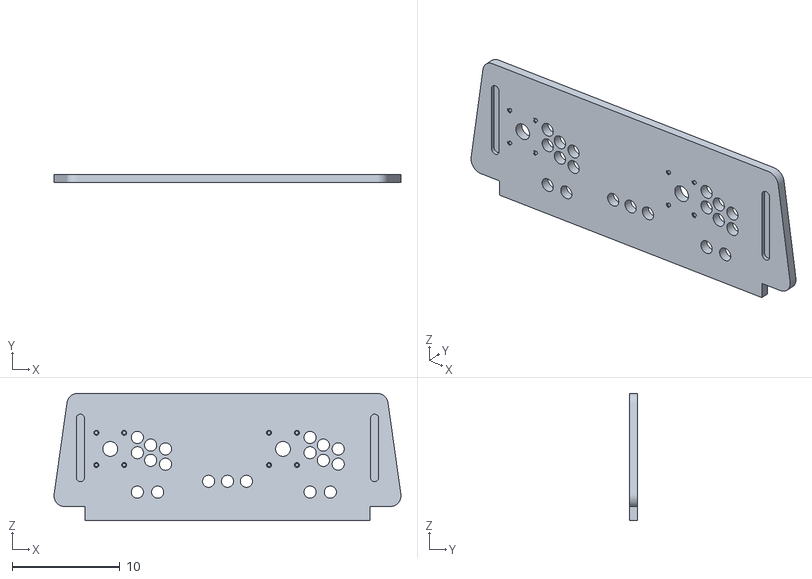
[picture p101: CAD file, 2020-04-03]
STLs and Gerbers/STL R1 for CNC (Manufactured)/Control Panel.STL
32.1 x 0.75 x 11.8
