pmgducati/Arcade-Project/STLs and Gerbers/STL R1 for CNC (Manufactured)/Sides - Left.STL

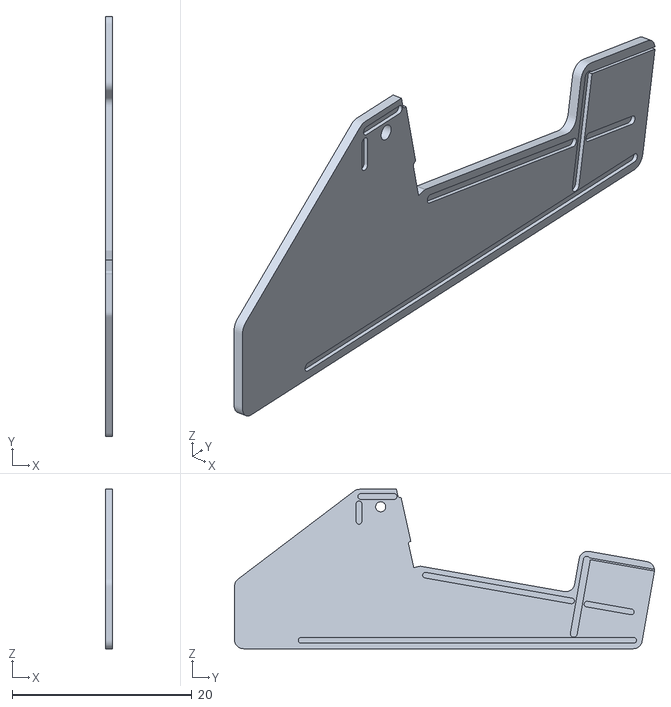
[picture p103: CAD file, 2020-04-03]
STLs and Gerbers/STL R1 for CNC (Manufactured)/Sides - Left.STL
0.75 x 46.7 x 17.8
