pmgducati/Arcade-Project/STLs and Gerbers/STL R2 (Updated)/Cleat - Inside Cabinet.DXF

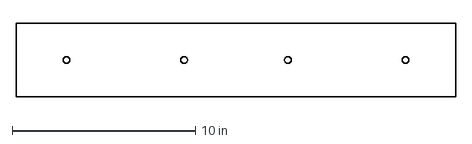
[picture p104: CAD file, 2025-06-07]
STLs and Gerbers/STL R2 (Updated)/Cleat - Inside Cabinet.DXF
24.0 x 4.00 in
