pmgducati/Arcade-Project/Art for Inspiration/AI Files/Decal Control Panel - NOHOLES.DXF

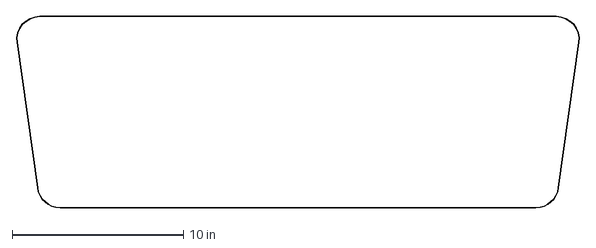
[picture p105: CAD file, 2020-04-03]
Art for Inspiration/AI Files/Decal Control Panel - NOHOLES.DXF
32.9 x 11.1 in
