pmgducati/Arcade-Project/CAD Files/Sides.SLDPRT

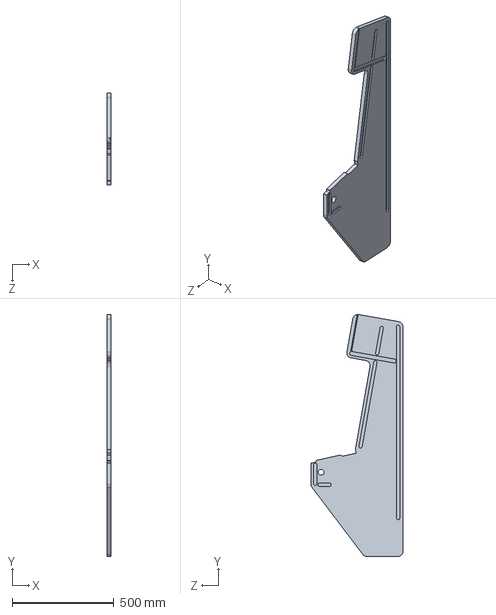
[picture p106: CAD file, 2026-02-07]
CAD Files/Sides.SLDPRT
19.1 x 1186.9 x 450.9 mm
