pmgducati/Arcade-Project/STLs and Gerbers/STL R1 for CNC (Manufactured)/Latch Mount.STL

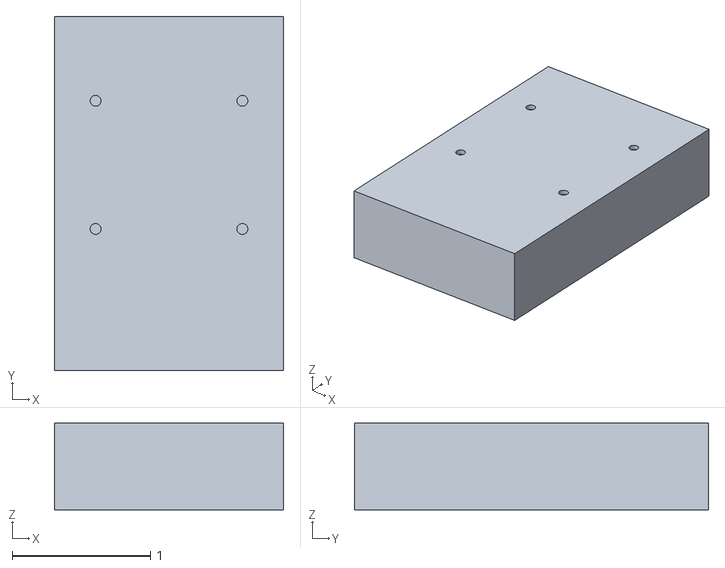
[picture p107: CAD file, 2020-04-03]
STLs and Gerbers/STL R1 for CNC (Manufactured)/Latch Mount.STL
1.65 x 2.56 x 0.625
