pmgducati/Arcade-Project/STLs and Gerbers/STL R2 (Updated)/Front Brace.DXF

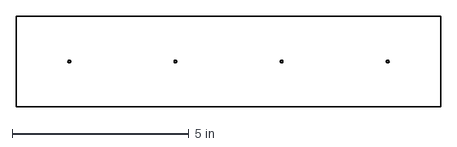
[picture p108: CAD file, 2025-06-07]
STLs and Gerbers/STL R2 (Updated)/Front Brace.DXF
12.0 x 2.56 in
