pmgducati/Arcade-Project/CAD Files/Control Panel.SLDPRT

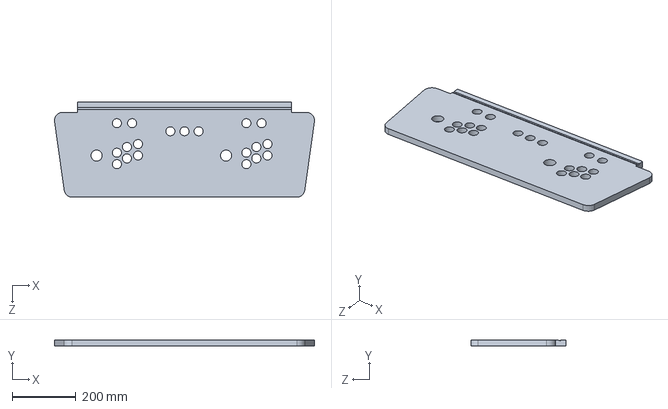
[picture p109: CAD file, 2026-02-07]
CAD Files/Control Panel.SLDPRT
816.2 x 19.1 x 299.5 mm
