pmgducati/Arcade-Project/STLs and Gerbers/STL R1 for CNC (Manufactured)/Cleat - Wall.STL

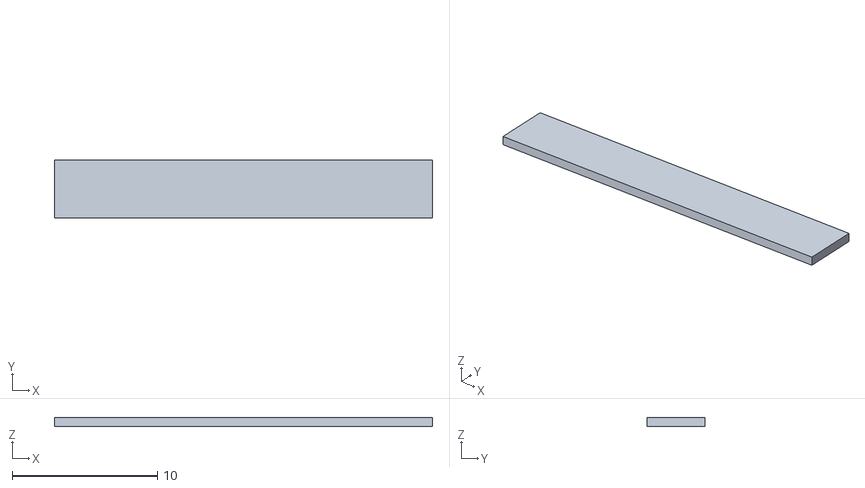
[picture p110: CAD file, 2020-04-03]
STLs and Gerbers/STL R1 for CNC (Manufactured)/Cleat - Wall.STL
26.0 x 4.00 x 0.625
