pmgducati/Arcade-Project/STLs and Gerbers/STL R2 (Updated)/Latch Mount.DXF

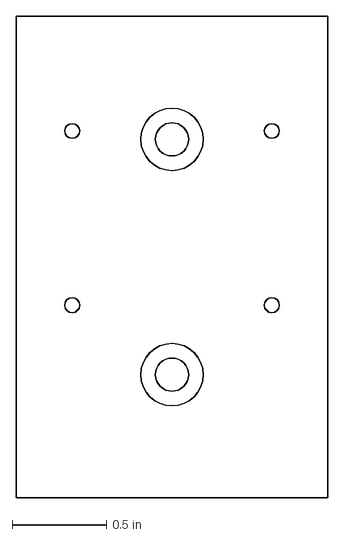
[picture p111: CAD file, 2025-06-07]
STLs and Gerbers/STL R2 (Updated)/Latch Mount.DXF
1.65 x 2.56 in
