pmgducati/Arcade-Project/CAD Files/Edgeband.SLDPRT

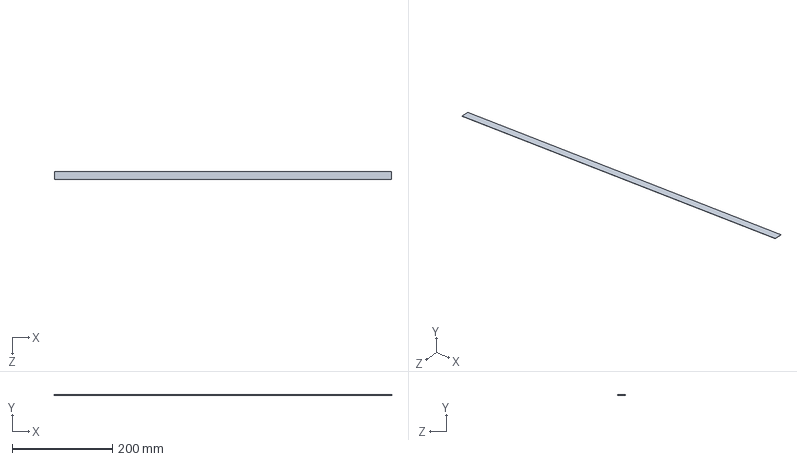
[picture p112: CAD file, 2026-02-07]
CAD Files/Edgeband.SLDPRT
673.1 x 0.457 x 15.9 mm
