pmgducati/Arcade-Project/STLs and Gerbers/STL R1 for CNC (Manufactured)/LED Panel.STL

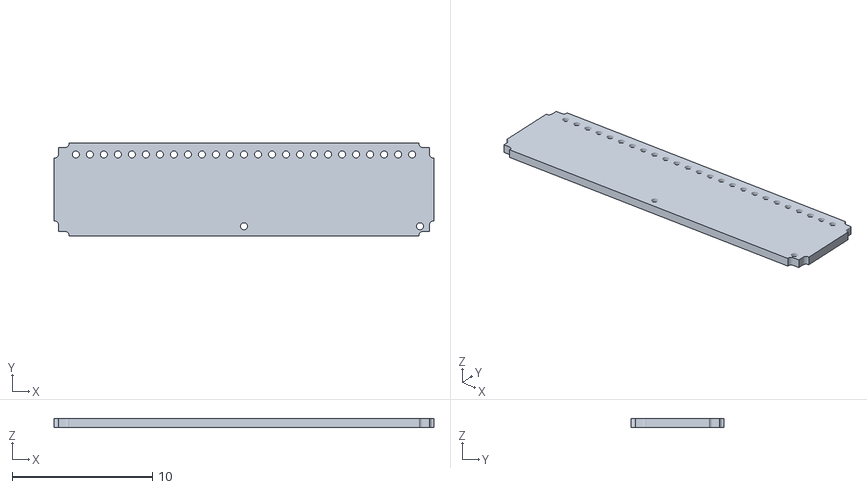
[picture p113: CAD file, 2020-04-03]
STLs and Gerbers/STL R1 for CNC (Manufactured)/LED Panel.STL
27.1 x 6.62 x 0.625
