pmgducati/Arcade-Project/STLs and Gerbers/STL R2 (Updated)/Monitor Brace Bracket Mount Secondary Plate.STL

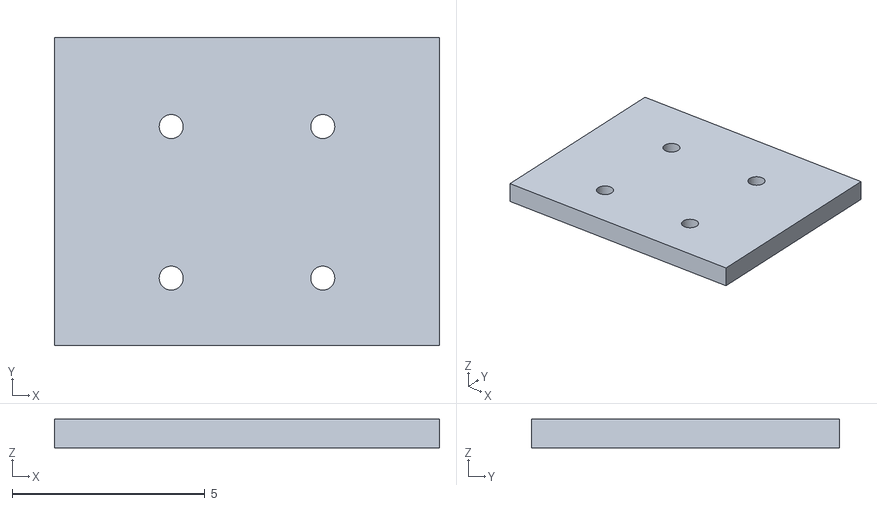
[picture p114: CAD file, 2020-11-29]
STLs and Gerbers/STL R2 (Updated)/Monitor Brace Bracket Mount Secondary Plate.STL
10.0 x 8.00 x 0.75
