pmgducati/Arcade-Project/CAD Files/Monitor Brace Bracket Mount.SLDPRT

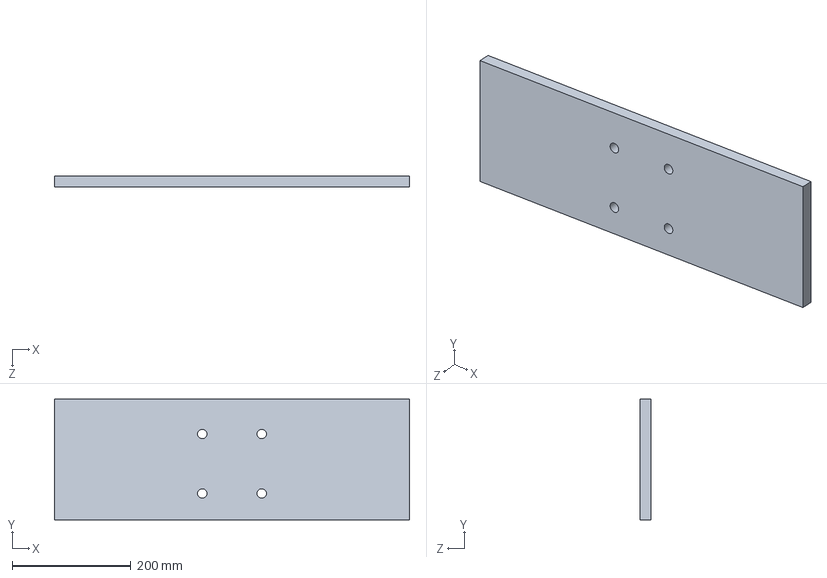
[picture p115: CAD file, 2025-06-07]
CAD Files/Monitor Brace Bracket Mount.SLDPRT
596.9 x 203.2 x 19.1 mm
