pmgducati/Arcade-Project/STLs and Gerbers/STL R1 for CNC (Manufactured)/Back.STL

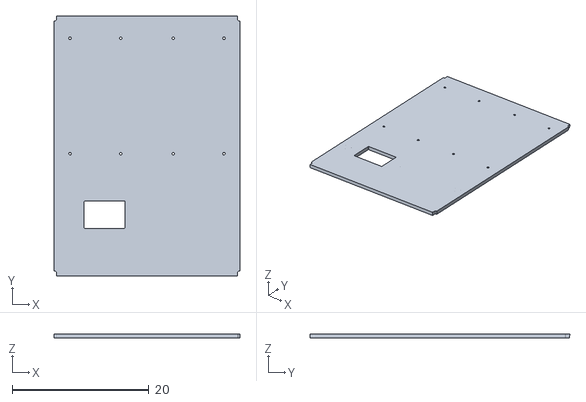
[picture p116: CAD file, 2020-04-03]
STLs and Gerbers/STL R1 for CNC (Manufactured)/Back.STL
27.1 x 38.0 x 0.625
