pmgducati/Arcade-Project/CAD Files/Front Panel.SLDPRT

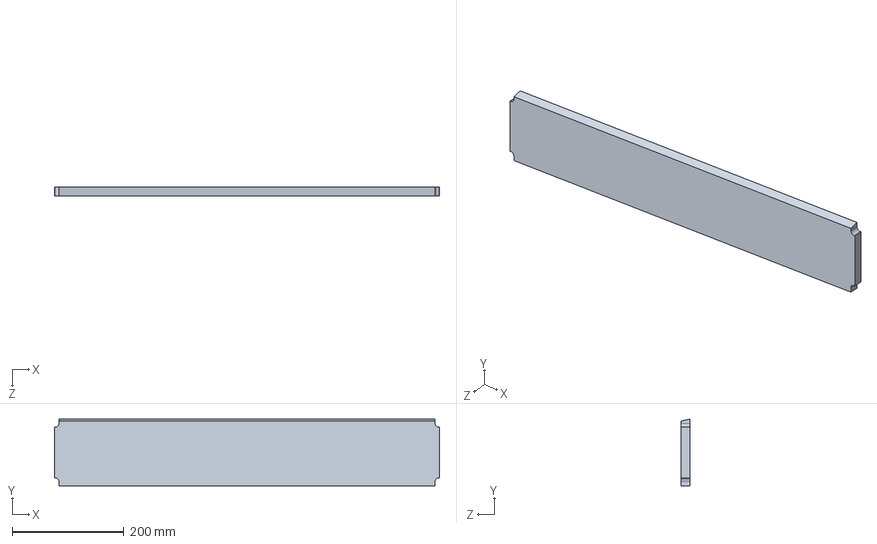
[picture p117: CAD file, 2025-06-07]
CAD Files/Front Panel.SLDPRT
689.0 x 119.6 x 15.9 mm
