pmgducati/Arcade-Project/STLs and Gerbers/STL R1 for CNC (Manufactured)/Top.STL

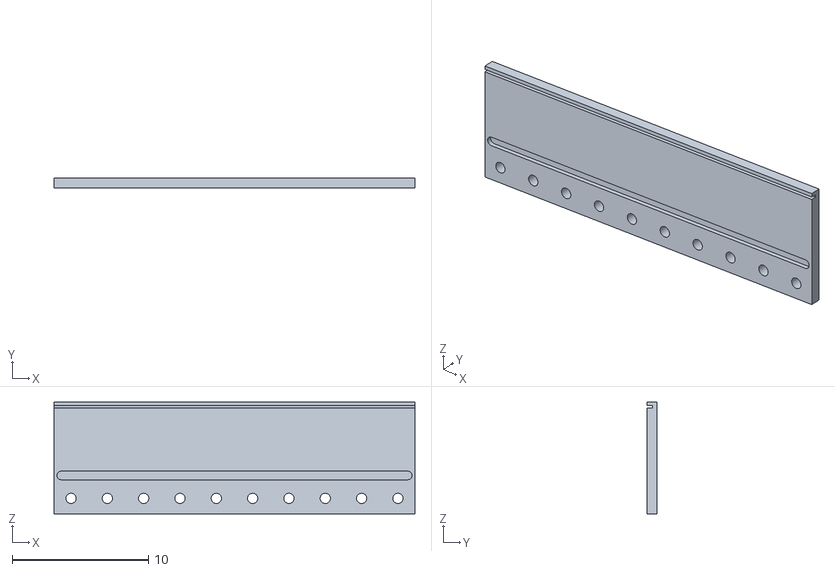
[picture p118: CAD file, 2020-04-03]
STLs and Gerbers/STL R1 for CNC (Manufactured)/Top.STL
26.5 x 0.75 x 8.19
