pmgducati/Arcade-Project/CAD Files/Speaker Panel.SLDPRT

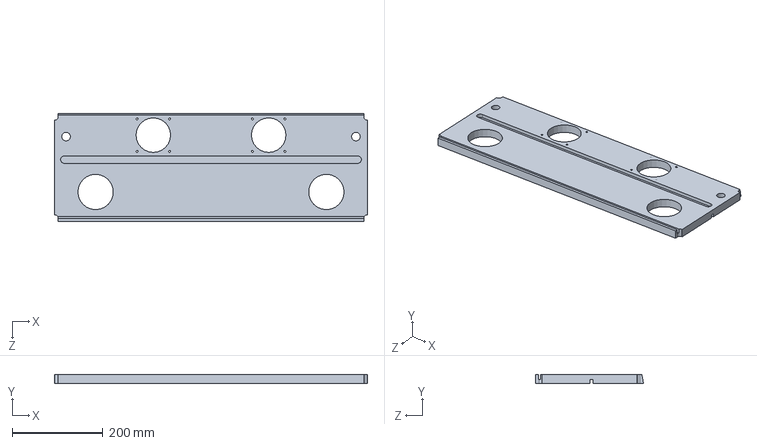
[picture p119: CAD file, 2025-06-07]
CAD Files/Speaker Panel.SLDPRT
689.0 x 19.1 x 237.7 mm
