pmgducati/Arcade-Project/STLs and Gerbers/STL R1 for CNC (Manufactured)/Latch Brace.STL

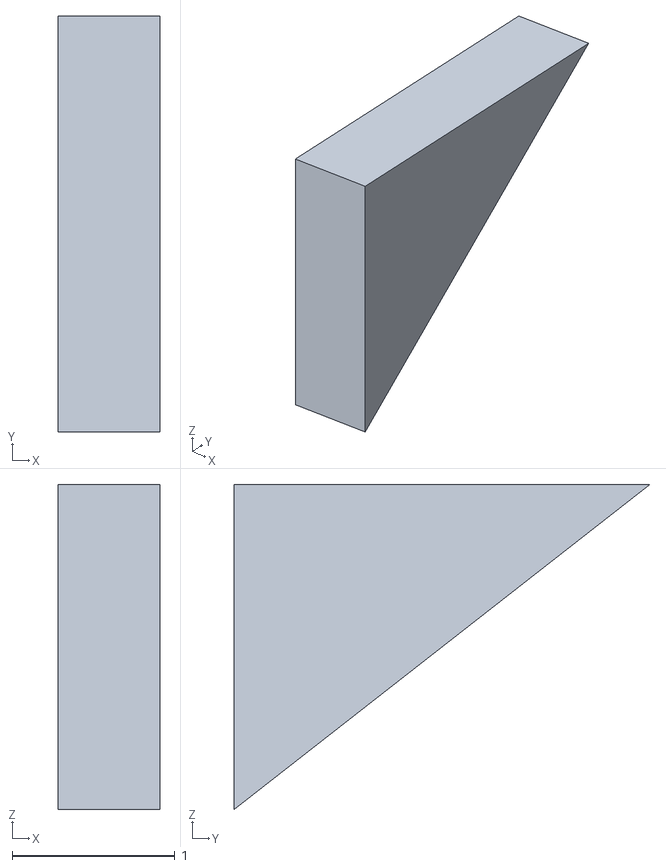
[picture p120: CAD file, 2020-04-03]
STLs and Gerbers/STL R1 for CNC (Manufactured)/Latch Brace.STL
0.625 x 2.56 x 2.00
