pmgducati/Arcade-Project/STLs and Gerbers/STL R2 (Updated)/Speaker Panel.STL

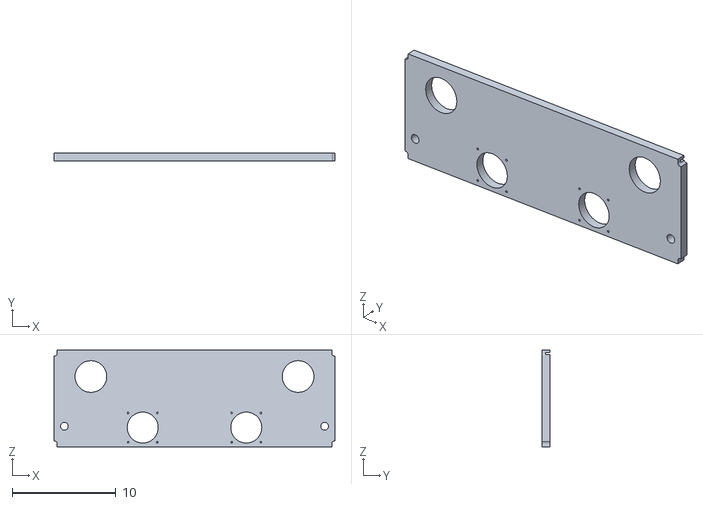
[picture p121: CAD file, 2020-11-29]
STLs and Gerbers/STL R2 (Updated)/Speaker Panel.STL
27.1 x 0.75 x 9.36
