pmgducati/Arcade-Project/CAD Files/LED Panel.SLDPRT

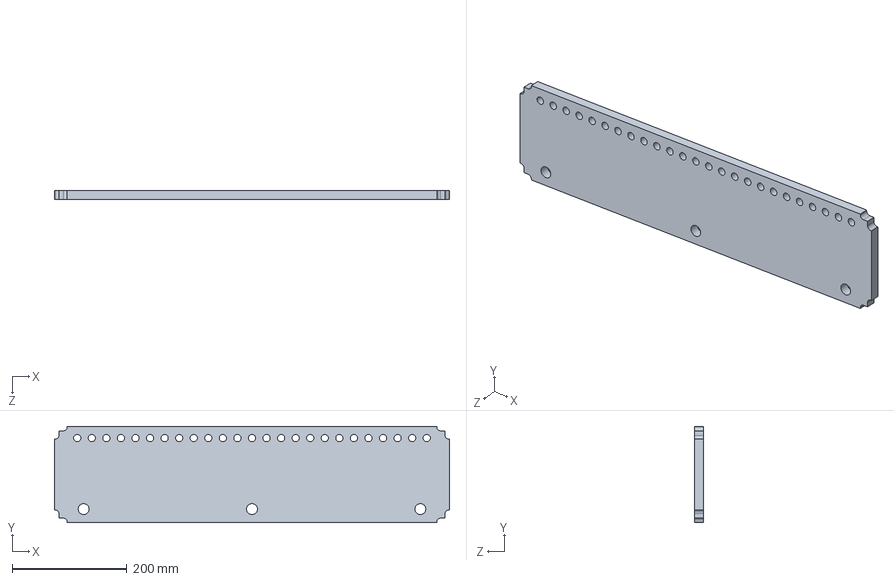
[picture p122: CAD file, 2025-06-07]
CAD Files/LED Panel.SLDPRT
689.0 x 168.3 x 15.9 mm
