pmgducati/Arcade-Project/CAD Files/Marquee Plexi.SLDPRT

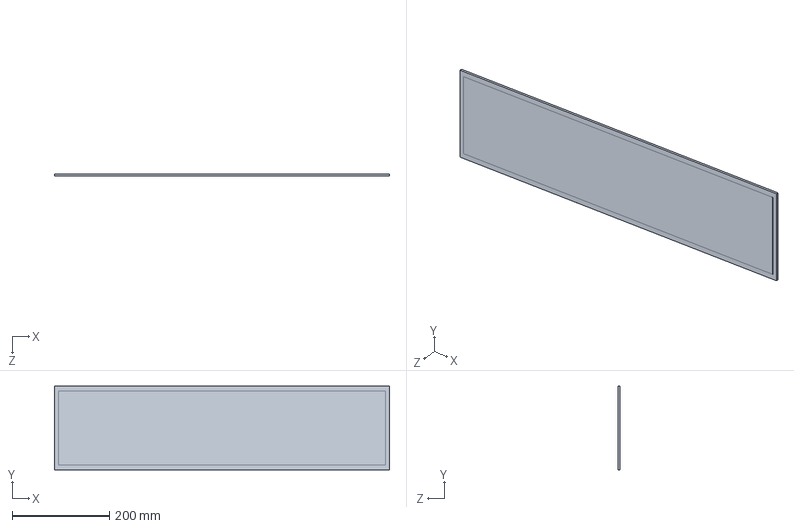
[picture p123: CAD file, 2025-06-07]
CAD Files/Marquee Plexi.SLDPRT
689.1 x 172.2 x 4.52 mm
