pmgducati/Arcade-Project/STLs and Gerbers/STL R1 for CNC (Manufactured)/Bottom Lip.STL

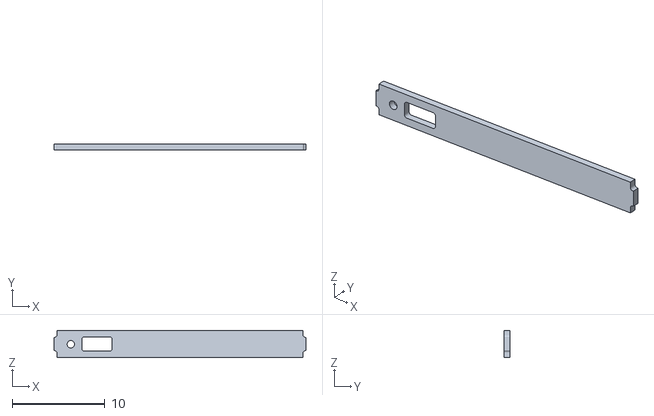
[picture p124: CAD file, 2020-04-03]
STLs and Gerbers/STL R1 for CNC (Manufactured)/Bottom Lip.STL
27.1 x 0.625 x 2.94
