pmgducati/Arcade-Project/STLs and Gerbers/STL R2 (Updated)/Top.STL

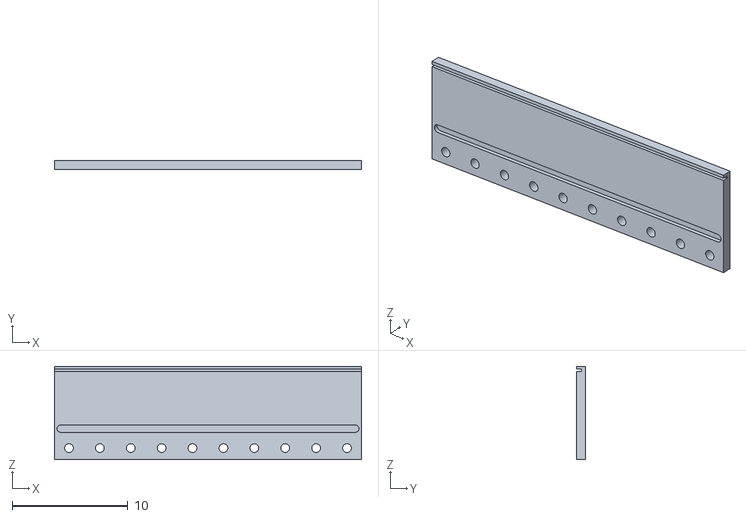
[picture p125: CAD file, 2020-11-29]
STLs and Gerbers/STL R2 (Updated)/Top.STL
26.5 x 0.75 x 8.06
