pmgducati/Arcade-Project/CAD Files/Monitor Panel.SLDPRT

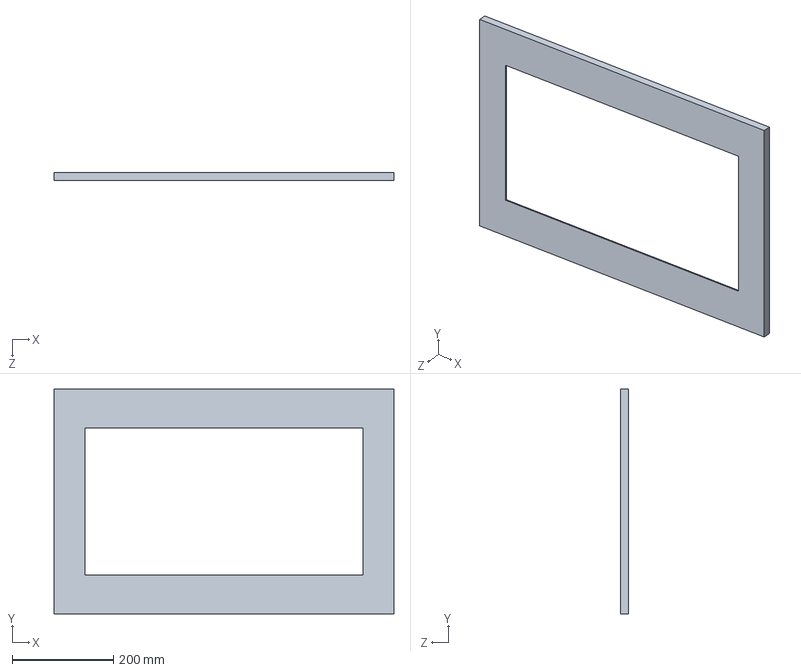
[picture p126: CAD file, 2025-06-07]
CAD Files/Monitor Panel.SLDPRT
673.1 x 444.5 x 15.9 mm
