pmgducati/Arcade-Project/STLs and Gerbers/STL R2 (Updated)/Monitor Brace Bracket Side.STL

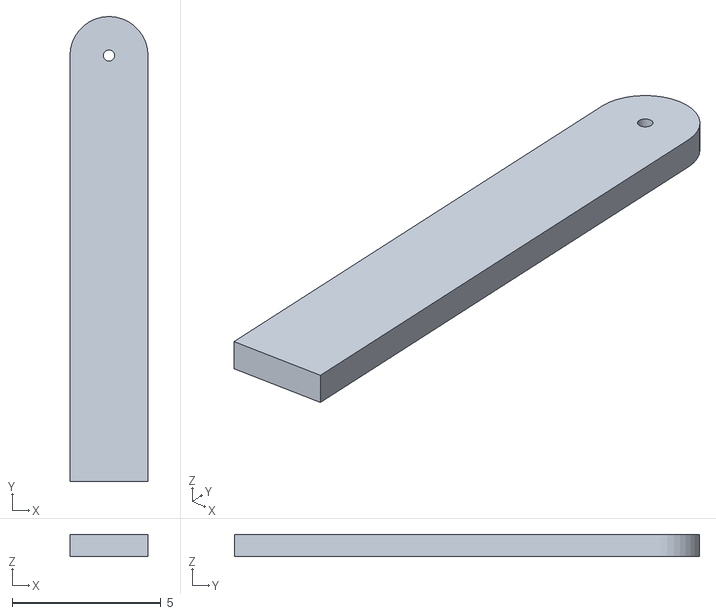
[picture p127: CAD file, 2020-11-29]
STLs and Gerbers/STL R2 (Updated)/Monitor Brace Bracket Side.STL
2.62 x 15.6 x 0.75
