pmgducati/Arcade-Project/CAD Files/Monitor Brace Side.SLDPRT

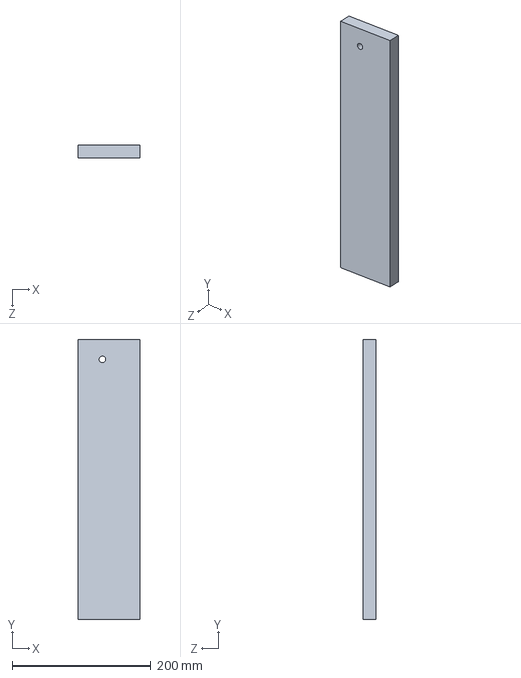
[picture p128: CAD file, 2025-06-07]
CAD Files/Monitor Brace Side.SLDPRT
88.9 x 403.2 x 19.1 mm
