pmgducati/Arcade-Project/STLs and Gerbers/STL R2 (Updated)/Monitor Brace Bracket Mount.STL

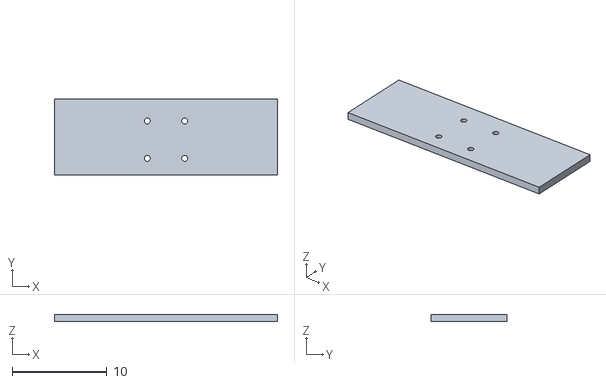
[picture p129: CAD file, 2020-11-29]
STLs and Gerbers/STL R2 (Updated)/Monitor Brace Bracket Mount.STL
23.5 x 8.00 x 0.75
