pmgducati/Arcade-Project/CAD Files/Monitor Brace Bracket Side.SLDPRT

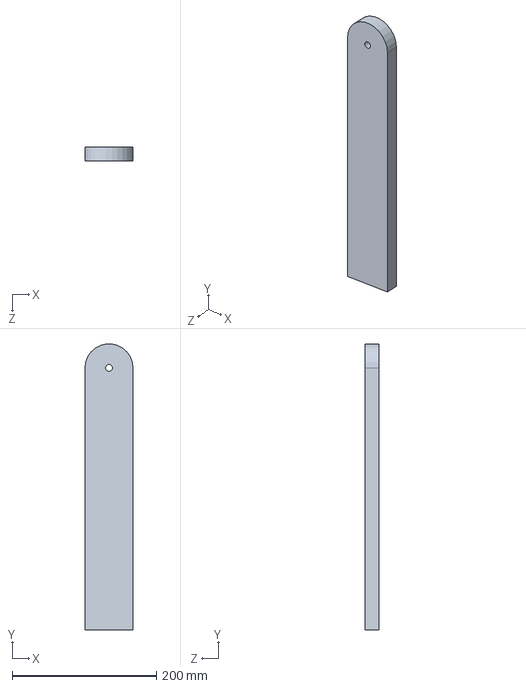
[picture p130: CAD file, 2025-06-07]
CAD Files/Monitor Brace Bracket Side.SLDPRT
66.7 x 396.6 x 19.1 mm
