pmgducati/Arcade-Project/STLs and Gerbers/STL R2 (Updated)/Monitor Brace Side.STL

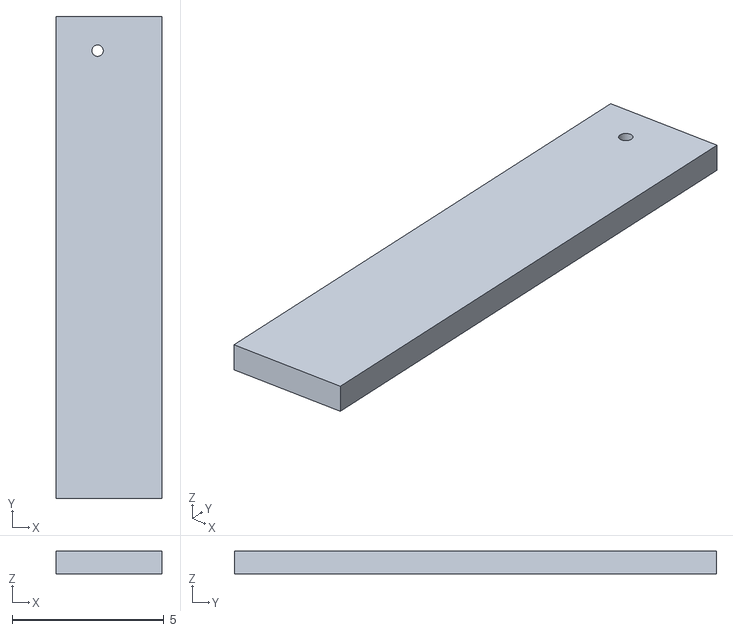
[picture p131: CAD file, 2020-11-29]
STLs and Gerbers/STL R2 (Updated)/Monitor Brace Side.STL
3.50 x 15.9 x 0.75
