pmgducati/Arcade-Project/CAD Files/Cleat.SLDPRT

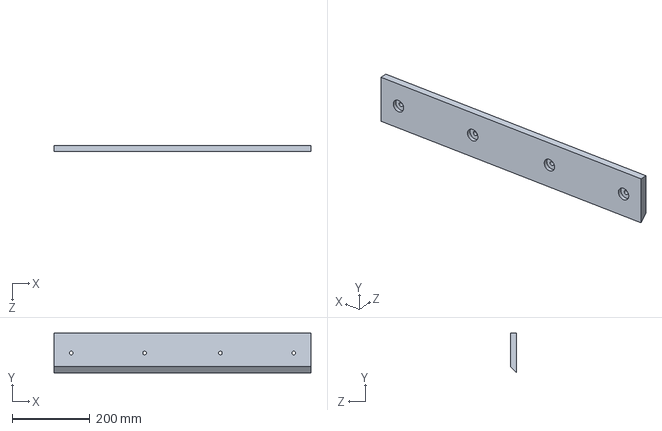
[picture p132: CAD file, 2025-06-07]
CAD Files/Cleat.SLDPRT
660.4 x 101.6 x 15.9 mm
