pmgducati/Arcade-Project/CAD Files/Back.SLDPRT

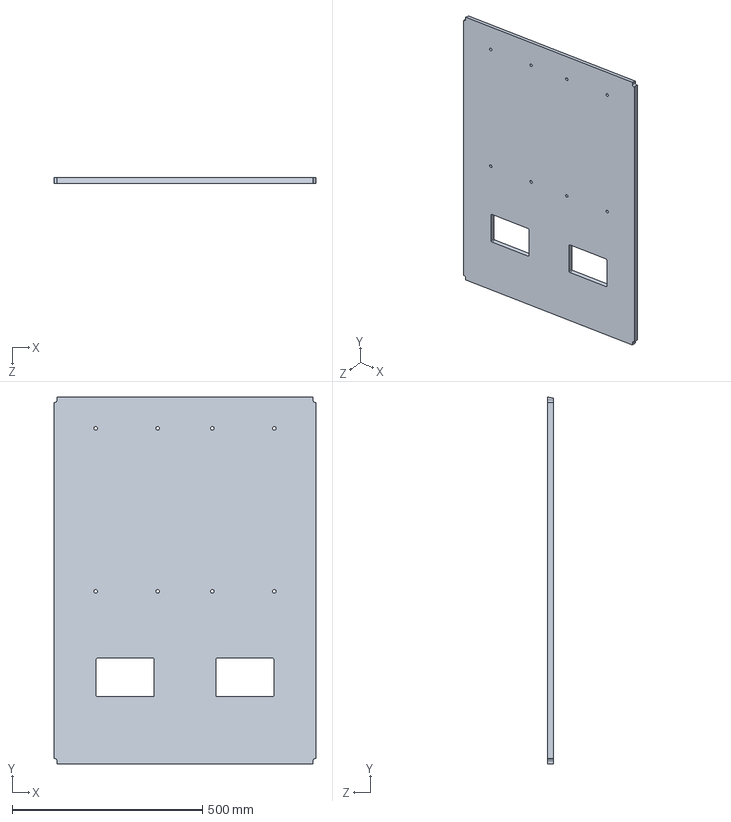
[picture p133: CAD file, 2025-06-07]
CAD Files/Back.SLDPRT
689.0 x 965.2 x 15.9 mm
