pmgducati/Arcade-Project/CAD Files/Front Brace.SLDPRT

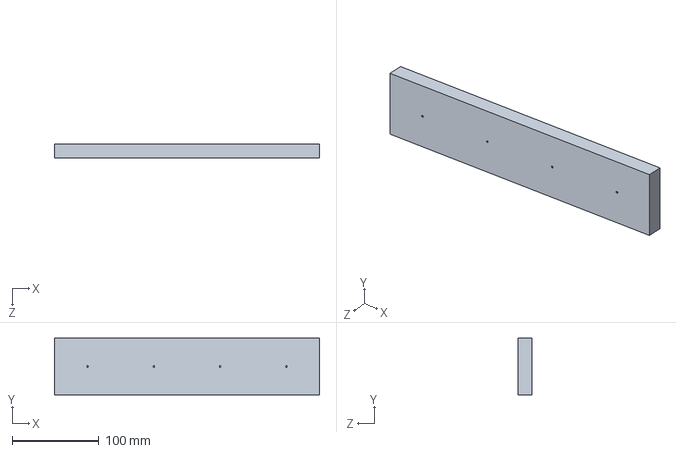
[picture p134: CAD file, 2025-06-07]
CAD Files/Front Brace.SLDPRT
304.8 x 65.0 x 15.9 mm
