pmgducati/Arcade-Project/CAD Files/Top.SLDPRT

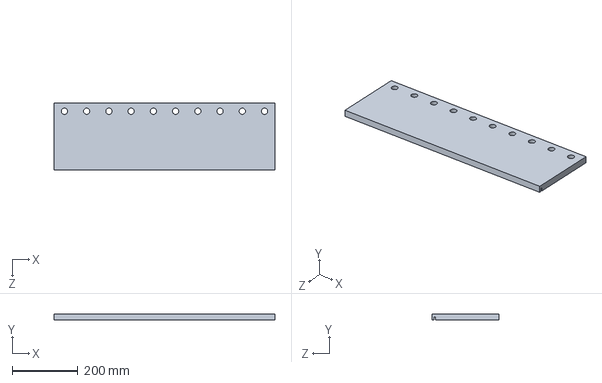
[picture p135: CAD file, 2025-06-07]
CAD Files/Top.SLDPRT
673.1 x 19.1 x 204.7 mm
