pmgducati/Arcade-Project/CAD Files/Latch Mount.SLDPRT

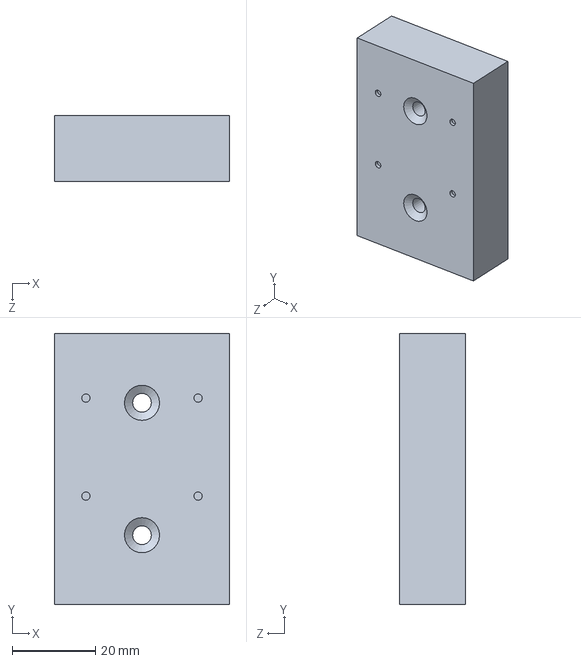
[picture p136: CAD file, 2025-06-07]
CAD Files/Latch Mount.SLDPRT
42.0 x 65.0 x 15.9 mm
