pmgducati/Arcade-Project/CAD Files/Bottom Lip.SLDPRT

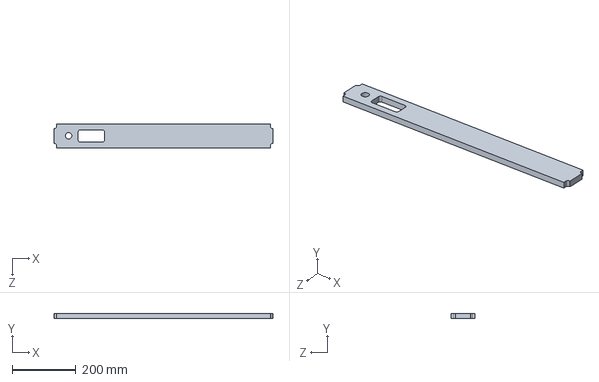
[picture p137: CAD file, 2025-06-07]
CAD Files/Bottom Lip.SLDPRT
689.0 x 15.9 x 74.7 mm
