pmgducati/Arcade-Project/CAD Files/LCD Mount.SLDPRT

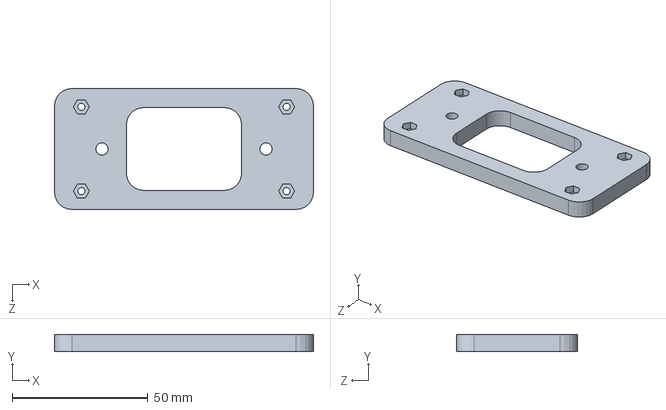
[picture p138: CAD file, 2021-04-09]
CAD Files/LCD Mount.SLDPRT
95.2 x 6.35 x 44.5 mm
