pmgducati/Arcade-Project/CAD Files/Decal Marquee.SLDPRT

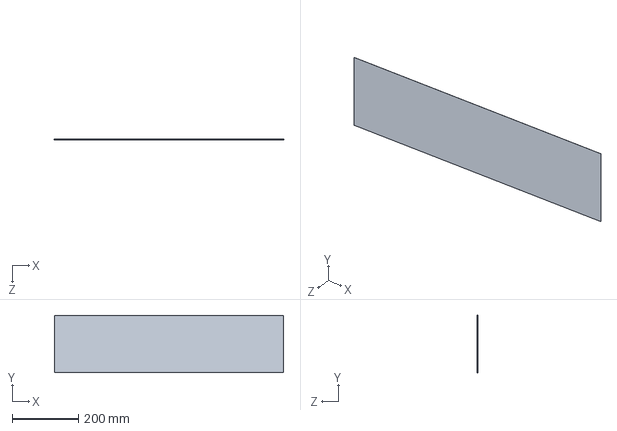
[picture p139: CAD file, 2020-04-03]
CAD Files/Decal Marquee.SLDPRT
689.1 x 172.2 x 0.203 mm
