pmgducati/Arcade-Project/CAD Files/Temp Brace.SLDPRT

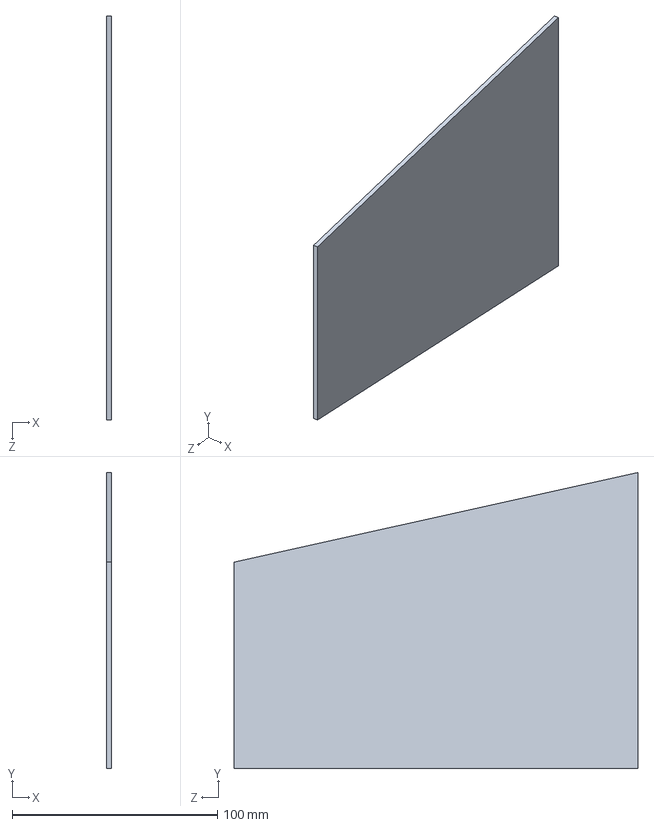
[picture p140: CAD file, 2020-04-03]
CAD Files/Temp Brace.SLDPRT
2.54 x 144.3 x 196.9 mm
