pmgducati/Arcade-Project/CAD Files/Decal Control Panel.SLDPRT

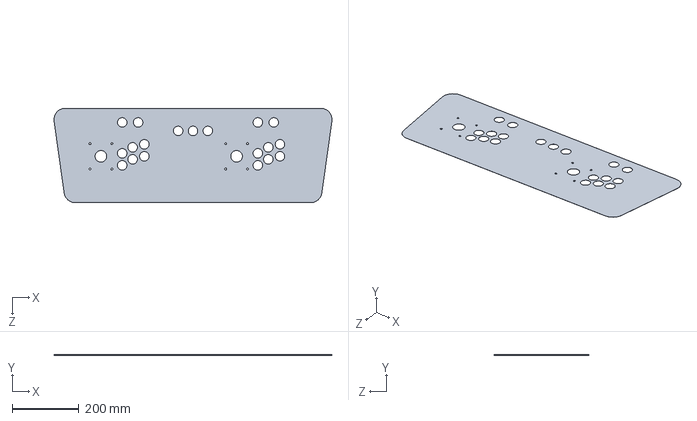
[picture p141: CAD file, 2020-04-03]
CAD Files/Decal Control Panel.SLDPRT
832.8 x 0.203 x 283.0 mm
