pmgducati/Arcade-Project/CAD Files/Decal Sides.SLDPRT

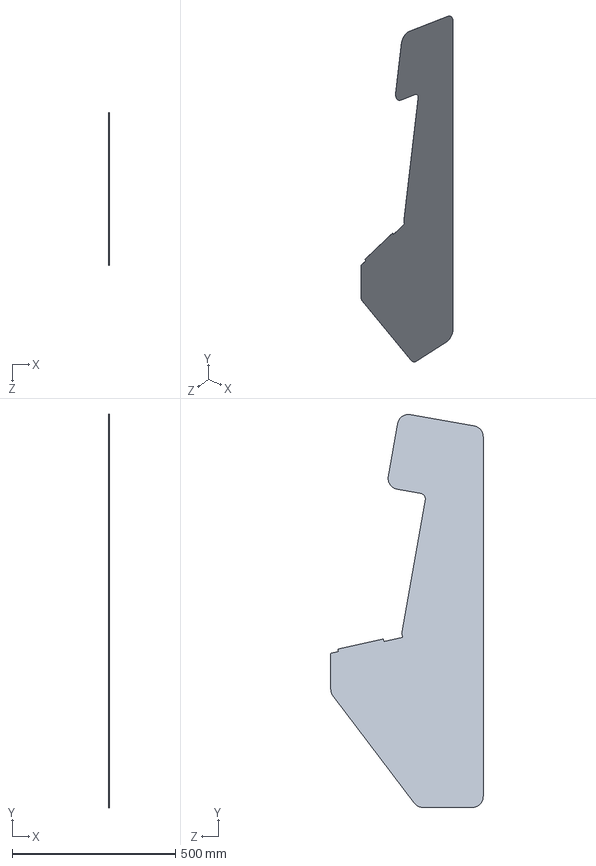
[picture p142: CAD file, 2020-04-03]
CAD Files/Decal Sides.SLDPRT
0.203 x 1202.7 x 466.7 mm
