pmgducati/Arcade-Project/CAD Files/Decal Bezel.SLDPRT

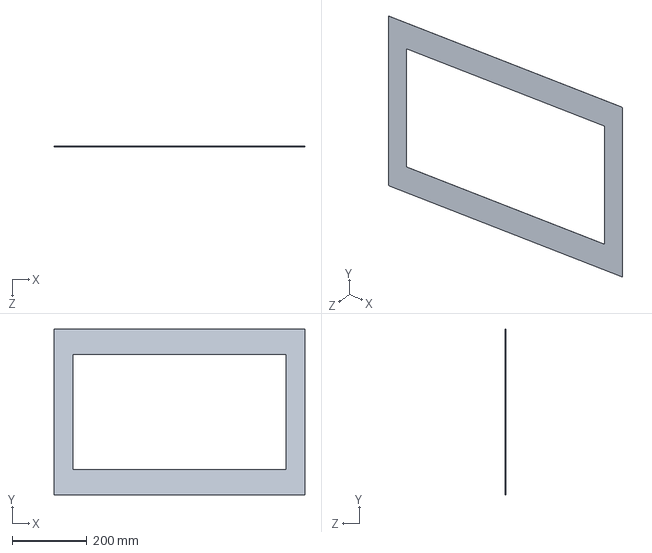
[picture p143: CAD file, 2020-04-03]
CAD Files/Decal Bezel.SLDPRT
673.1 x 444.5 x 0.203 mm
