pmgducati/Arcade-Project/Art for Inspiration/2.jpg

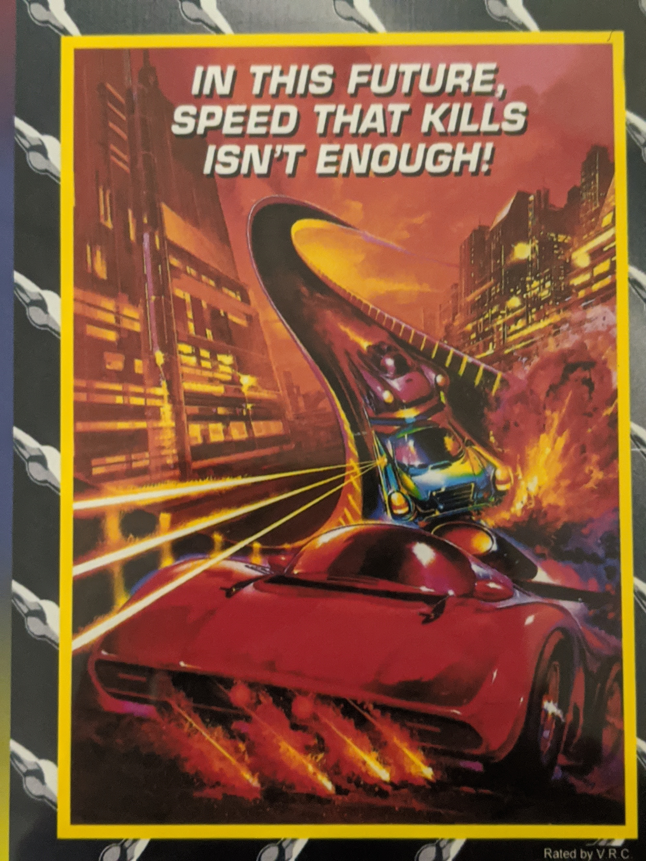
Art for Inspiration/2.jpg
