pmgducati/Arcade-Project/Art for Inspiration/4.jpg

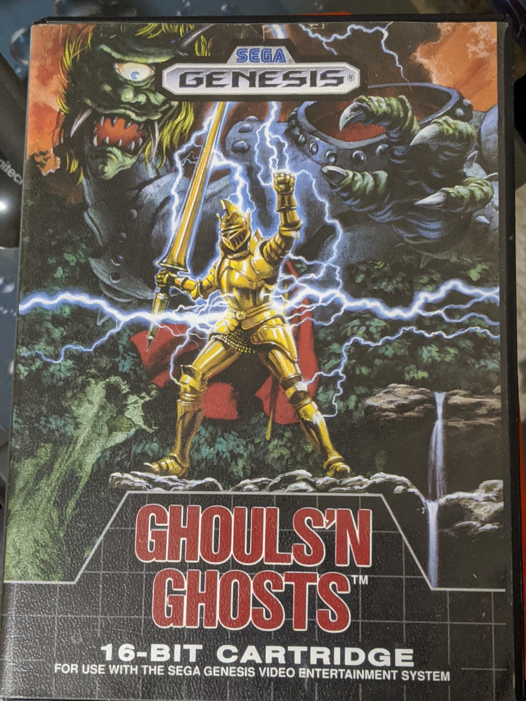
Art for Inspiration/4.jpg
