pmgducati/Arcade-Project/Art for Inspiration/5.jpg

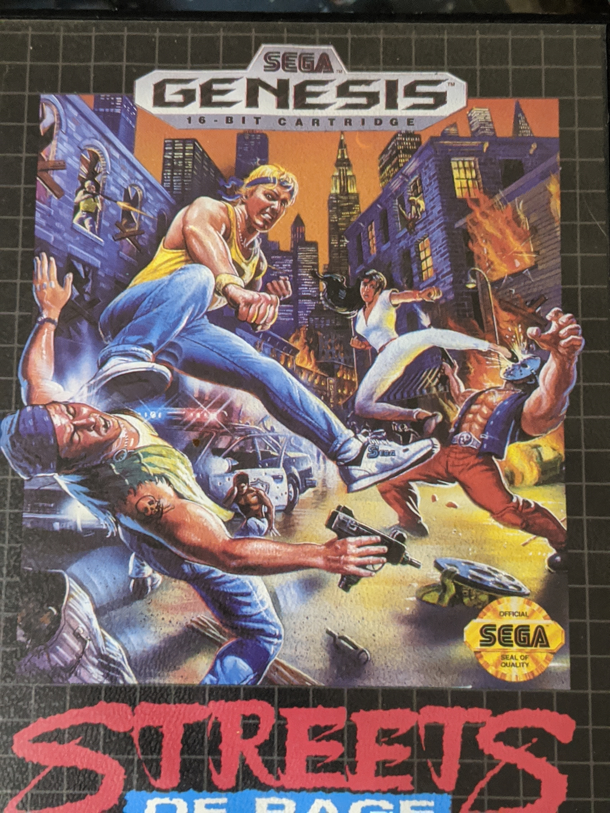
Art for Inspiration/5.jpg
