pmgducati/Arcade-Project/Art for Inspiration/6.jpg

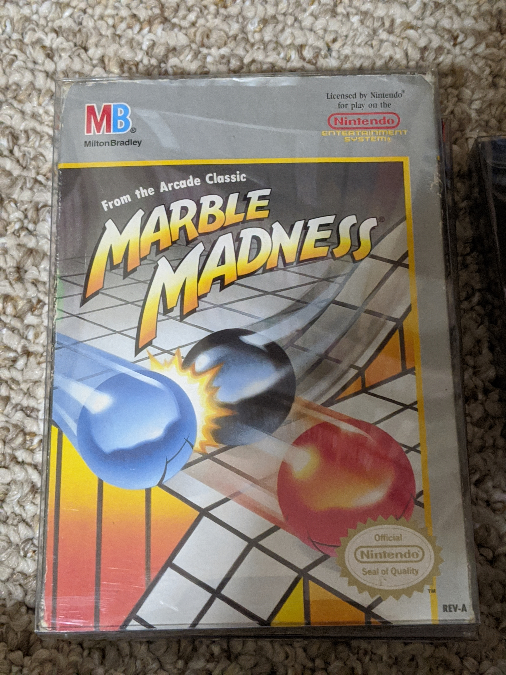
Art for Inspiration/6.jpg
