pmgducati/Arcade-Project/Art for Inspiration/7.jpg

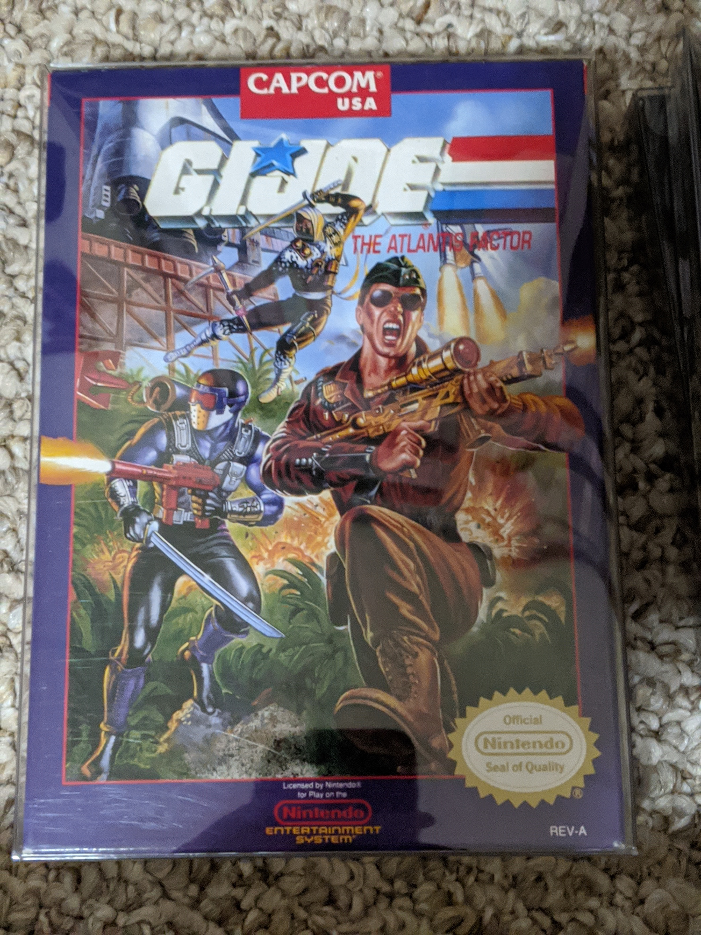
Art for Inspiration/7.jpg
