pmgducati/Arcade-Project/Art for Inspiration/8.jpg

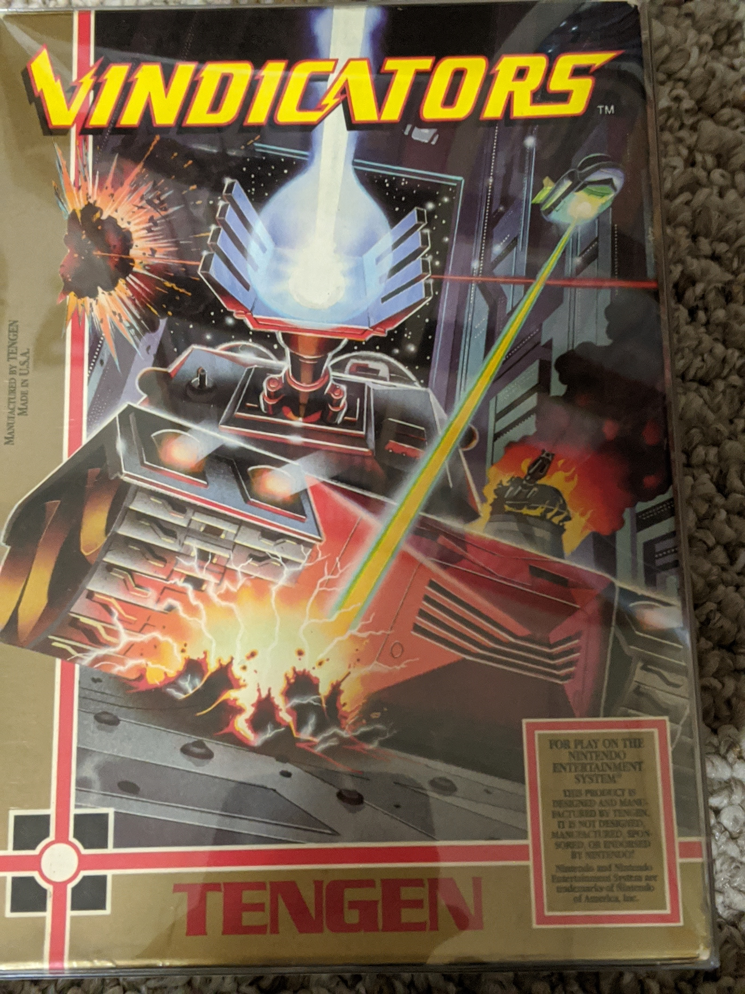
Art for Inspiration/8.jpg
