pmgducati/Arcade-Project/Art for Inspiration/9.jpg

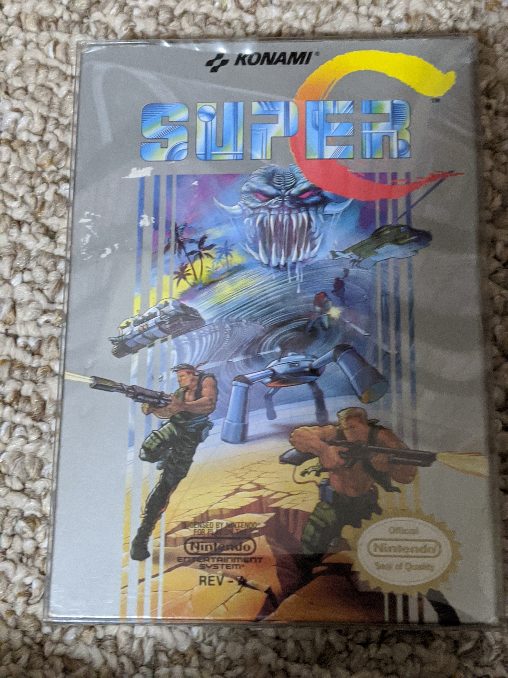
Art for Inspiration/9.jpg
