pmgducati/Arcade-Project/Art for Inspiration/50.jpg

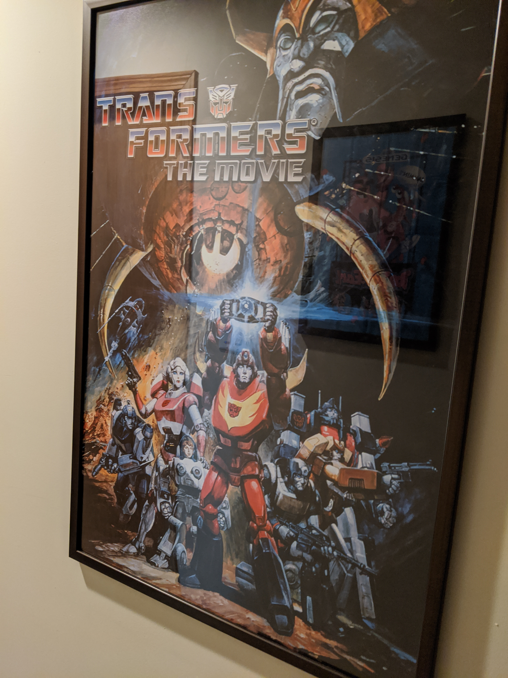
Art for Inspiration/50.jpg
