pmgducati/Arcade-Project/Art for Inspiration/61.jpg

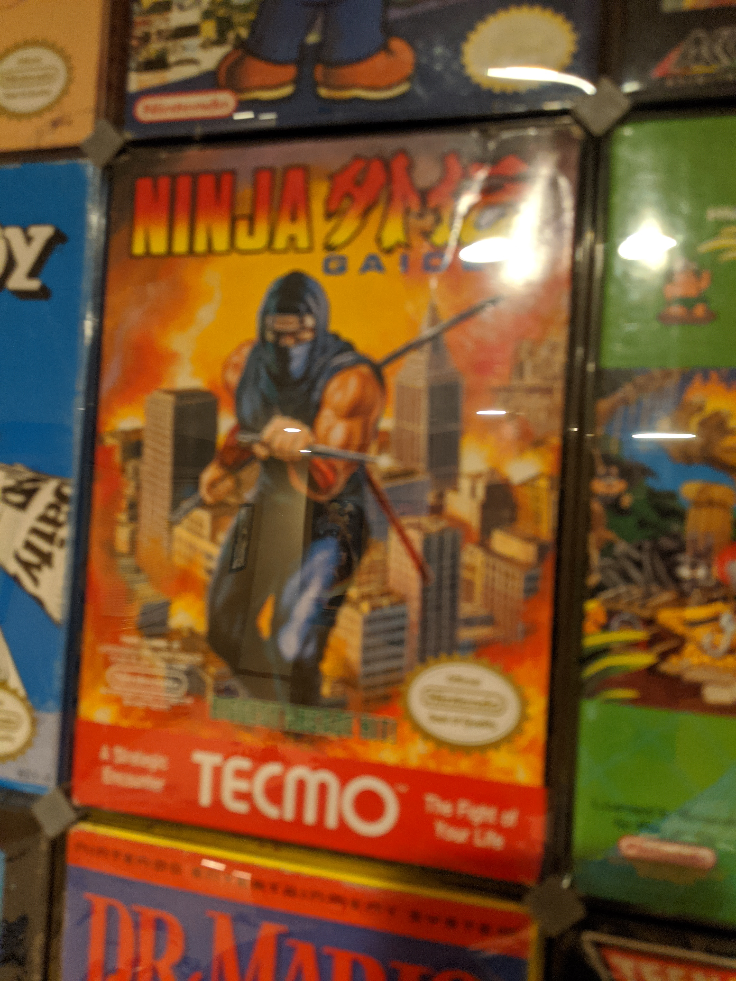
Art for Inspiration/61.jpg
