pmgducati/Arcade-Project/Art for Inspiration/81.jpg

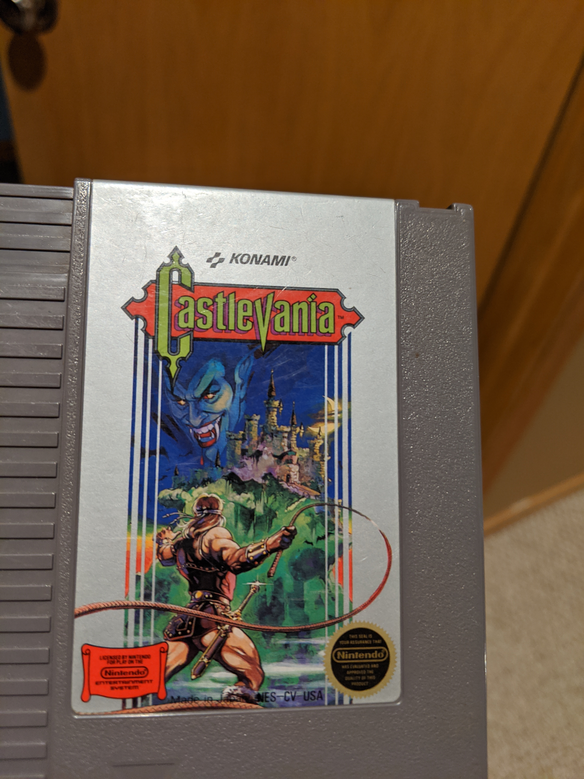
Art for Inspiration/81.jpg
