pmgducati/Arcade-Project/Art for Inspiration/82.jpg

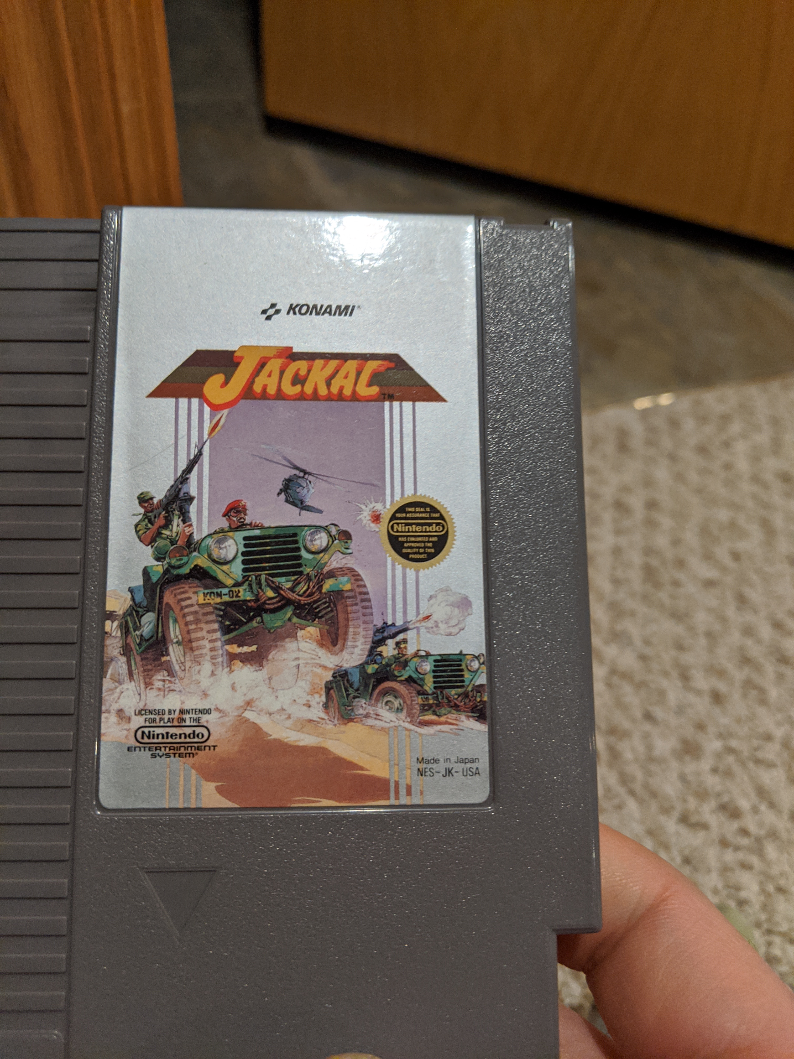
Art for Inspiration/82.jpg
