pmgducati/Arcade-Project/Art for Inspiration/84.jpg

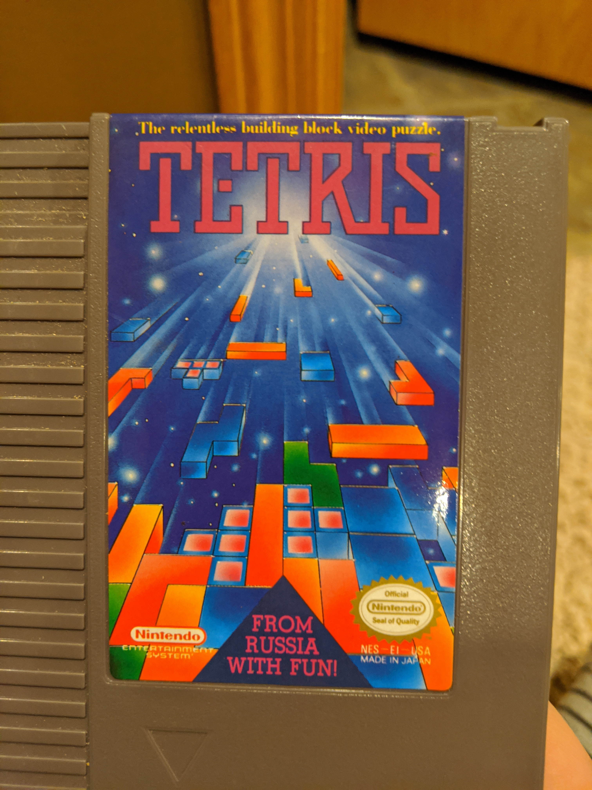
Art for Inspiration/84.jpg
